Ali-Z0/2221_Underwater-Positioning-System/hard/3.3to5V.pdf

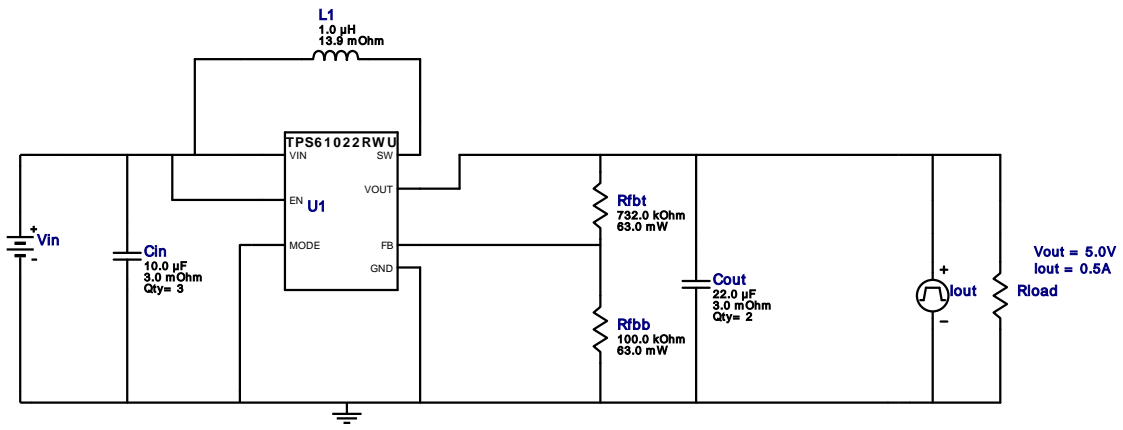
[picture p136: figure]
Vout = 5.0V Iout = 0.5A Cout; 22.0 µF 3.0 m Ohm Qty= 2; Rfbt 732.0 kOhm 63.0 m W; TPS6 1 0 2 2 RW U; GND; VOUT; MODE; VIN; Cin 10.0 µF 3.0 m Ohm Qty= 3; Rfbb 100.0 kOhm 63.0 m W; L1 1.0 µH 13.9 m Ohm; Vin; Iout; Rload

Copyright © 2023, Texas Instruments Incorporated | 1 | ti.com/webench

WEBENCH®
Design Report TPS61022RWUR : TPS61022RWUR 1V-3.7V to 5.00V @ 0.5A January 18, 2023 11:56:08 GMT-06:00

## WEBENCH ® Design Report

Design : 1 TPS61022RWUR
TPS61022RWUR 1V-3.7V to 5.00V @ 0.5A

VinMin = 1.0V
VinMax = 3.7V
Vout = 5.0V
Iout = 0.5A

Device = TPS61022RWUR
Topology = Boost_PassThrough Created = 2023-01-18 11:53:58.655 BOM Cost = $1.14
BOM Count = 9
Total Pd = 0.33W

### Design Alerts

Component Selection Information
1. The TPS61022 Device will operate in Pass-Through mode when Vin is greater than Vout. In Pass-Through mode, Vout is not regulated to the set Vout, instead Vout is Vin with the drop across the FET’s on-resistance and the DCR of the inductor. 2. This is a Boost Converter with 0.5V ultra-low input voltage. 3. The efficiency validation is done only for FPWM mode. Charts may be inaccurate for AutoMode at light loads and hence they are disabled for light loads.

## Electrical BOM

Name | Manufacturer | Part Number | Properties | Qty Price | Footprint
Cin | Kemet | C0805C106K8PACTU (http://capacitoredge.kemet.com/capedge2/DataSheet/Datasheet%2DC0805C106K8PACTU.pdf?pn%3DC0805C106K8PACTU) Series= X5R | Cap= 10.0 uF ESR= 3.0 mOhm VDC= 10.0 V IRMS= 11.43 A
3 | $0.03
| | | | | 0805 7 mm²
Cout | MuRata | GRM21BR61A226ME44L Series= X5R

Cap= 22.0 uF
ESR= 3.0 mOhm
VDC= 10.0 V
IRMS= 3.84 A

2 $0.09
0805 7 mm²
L1 | Bourns | SRN6045-1R0Y (http://www.bourns.com/data/global/pdfs/SRN6045.pdf) | L= 1.0 µH 13.9 mOhm | 1 | $0.25

SRN6045 64 mm²
Rfbb | Vishay-Dale | CRCW0402100KFKED (http://www.vishay.com/docs/20035/dcrcwe3.pdf) Series= CRCW..e3 | Res= 100.0 kOhm Power= 63.0 mW Tolerance= 1.0% | 1 | $0.01
0402 3 mm²
Rfbt | Vishay-Dale | CRCW0402732KFKED (http://www.vishay.com/docs/20035/dcrcwe3.pdf) Series= CRCW..e3 | Res= 732.0 kOhm Power= 63.0 mW Tolerance= 1.0% | 1 | $0.01
0402 3 mm²
U1 | Texas Instruments | TPS61022RWUR (http://www.ti.com/product/TPS61022) | Switcher | 1 | $0.60
RWU0007A 9 mm²

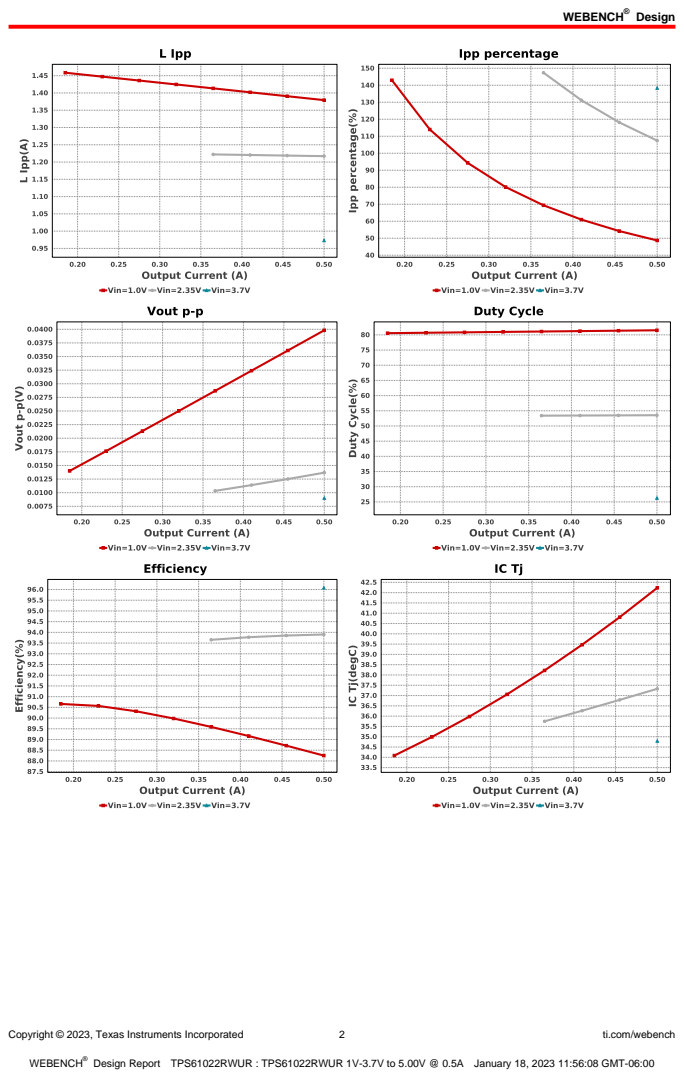
[picture p137: page 2]
Design; Copyright © 2023, Texas Instruments Incorporated; ti.com/webench

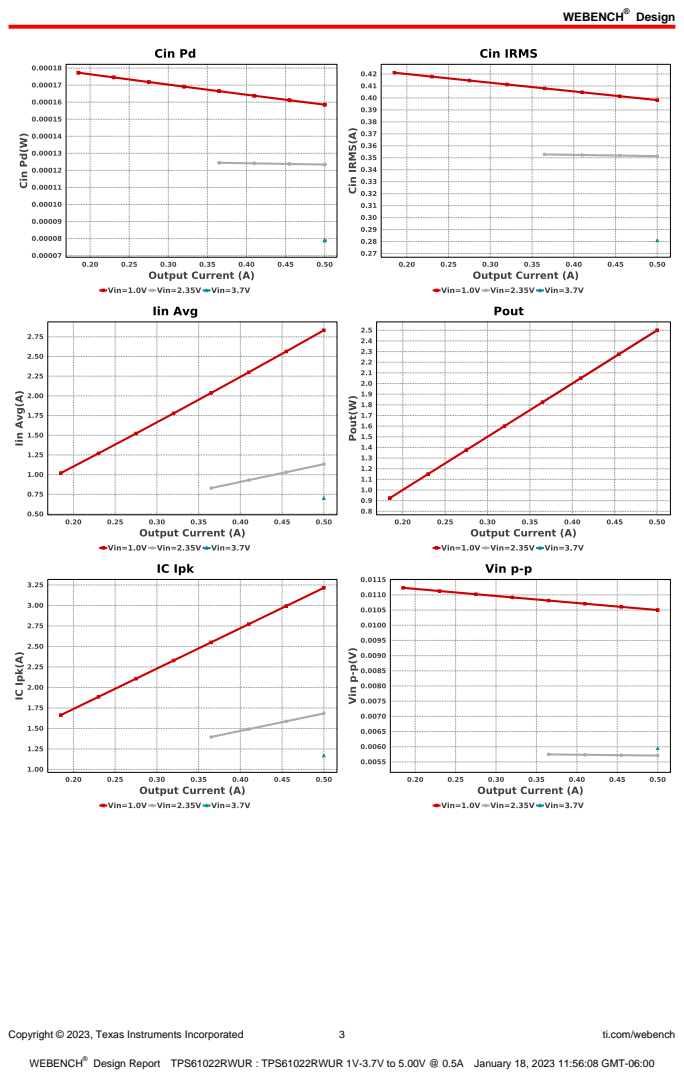
[picture p138: page 3]
Copyright © 2023, Texas Instruments Incorporated; ti.com/webench

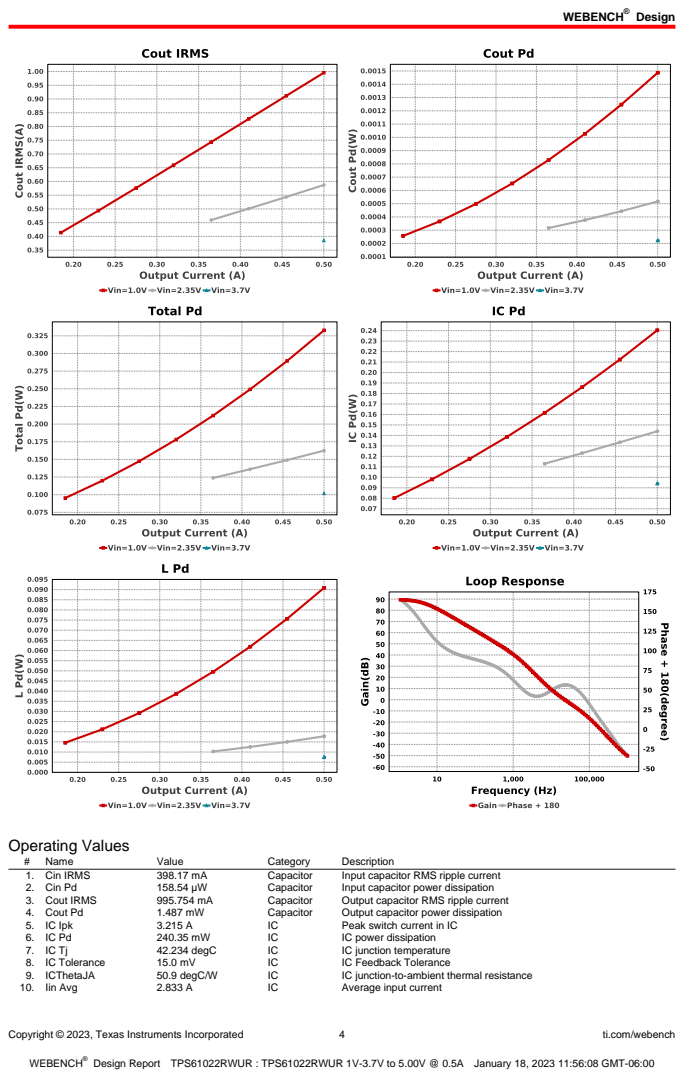
[picture p139: page 4]
Copyright © 2023, Texas Instruments Incorporated; ti.com/webench; Operating Values; Name; Value; Category; Description; 1. Cin IRMS; Capacitor; Input capacitor RMS ripple current; 2. Cin Pd; Input capacitor power dissipation; 3. Cout IRMS; Output capacitor RMS ripple current; 4. Cout Pd; Output capacitor power dissipation; 5. IC Ipk; Peak switch current in IC; IC power dissipation; 42.234 degC; IC junction temperature; 8. IC Tolerance; IC Feedback Tolerance; 9. ICThetaJA; 50.9 degC/W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

Copyright © 2023, Texas Instruments Incorporated | 5 | ti.com/webench
# | Name | Value | Category | Description

11. Ipp percentage | 48.689 % | Inductor | Inductor ripple current percentage (with respect to average inductor
| | | | current)
12. L Ipp | 1.379 A | Inductor | Peak-to-peak inductor ripple current
13. L Pd | 90.845 mW | Inductor | Inductor power dissipation
14. Cin Pd | 158.54 µW | Power | Input capacitor power dissipation
15. Cout Pd | 1.487 mW | Power | Output capacitor power dissipation
16. IC Pd | 240.35 mW | Power | IC power dissipation
17. L Pd | 90.845 mW | Power | Inductor power dissipation
18. Total Pd | 332.866 mW | Power | Total Power Dissipation
19. BOM Count | 9 | System
| | | Information | Total Design BOM count
20. Cross Freq | 8.104 kHz | System
| | | Information | Bode plot crossover frequency
21. Duty Cycle | 81.51 % | System
| | | Information | Duty cycle
22. Efficiency | 88.25 % | System
| | | Information | Steady state efficiency
23. FootPrint | 113.0 mm² | System
| | | Information | Total Foot Print Area of BOM components
24. Frequency | 541.532 kHz | System
| | | Information | Switching frequency
25. Gain Marg | -19.195 dB | System
| | | Information | Bode Plot Gain Margin
26. Iout | 500.0 mA | System
| | | Information | Iout operating point
27. Low Freq Gain | 77.425 dB | System
| | | Information | Gain at 1Hz
28. Mode | CCM | System
| | | Information | Conduction Mode
29. Phase Marg | 39.131 deg | System
| | | Information | Bode Plot Phase Margin
30. Pout | 2.5 W | System
| | | Information | Total output power
31. Total BOM | $1.14 | System
| | | Information | Total BOM Cost
32. Vin | 1.0 V | System
| | | Information | Vin operating point
33. Vin p-p | 10.502 mV | System
| | | Information | Peak-to-peak input voltage
34. Vout | 5.0 V | System
| | | Information | Operational Output Voltage
35. Vout Actual | 4.992 V | System
| | | Information | Vout Actual calculated based on selected voltage divider resistors
36. Vout Tolerance | 4.322 % | System
| | | Information | Vout Tolerance based on IC Tolerance (no load) and voltage divider resistors if applicable
37. Vout p-p | 39.821 mV | System
| | | Information | Peak-to-peak output ripple voltage

## Design Inputs

Name | Value | Description
| Iout | | 500.0 m | Maximum Output Current
VinMax | 3.7 | Maximum input voltage
VinMin | 1.0 | Minimum input voltage
Vout | 5.0 | Output Voltage
| base_pn | | TPS61022 | Base Product Number
source | DC | Input Source Type
Ta | 30.0 | Ambient temperature


Copyright © 2023, Texas Instruments Incorporated | 6 | ti.com/webench

## Assembly

## Component Testing

Some published data on components in datasheets such as Capacitor ESR and Inductor DC resistance is based on conservative values that will guarantee that the components always exceed the specification. For design purposes it is usually better to work with typical values. Since this data is not always available it is a good practice to measure the Capacitance and ESR values of Cin and Cout, and the inductance and DC resistance of L1 before assembly of the board. Any large discrepancies in values should be electrically simulated in WEBENCH to check for instabilities and thermally simulated in WebTHERM to make sure critical temperatures are not exceeded.

## Soldering Component to Board

If board assembly is done in house it is best to tack down one terminal of a component on the board then solder the other terminal. For surface mount parts with large tabs, such as the DPAK, the tab on the back of the package should be pre-tinned with solder, then tacked into place by one of the pins. To solder the tab town to the board place the iron down on the board while resting against the tab, heating both surfaces simultaneously. Apply light pressure to the top of the plastic case until the solder flows around the part and the part is flush with the PCB. If the solder is not flowing around the board you may need a higher wattage iron (generally 25W to 30W is enough).

## Initial Startup of Circuit

It is best to initially power up the board by setting the input supply voltage to the lowest operating input voltage 1.0V and set the input supply's current limit to zero. With the input supply off connect up the input supply to Vin and GND. Connect a digital volt meter and a load if needed to set the minimum Iout of the design from Vout and GND. Turn on the input supply and slowly turn up the current limit on the input supply. If the voltage starts to rise on the input supply continue increasing the input supply current limit while watching the output voltage. If the current increases on the input supply, but the voltage remains near zero, then there may be a short or a component misplaced on the board. Power down the board and visually inspect for solder bridges and recheck the diode and capacitor polarities. Once the power supply circuit is operational then more extensive testing may include full load testing, transient load and line tests to compare with simulation results.

## Load Testing

The setup is the same as the initial startup, except that an additional digital voltmeter is connected between Vin and GND, a load is connected between Vout and GND and a current meter is connected in series between Vout and the load. The load must be able to handle at least rated output power + 50% ( 7.5 watts for this design). Ideally the load is supplied in the form of a variable load test unit. It can also be done in the form of suitably large power resistors. When using an oscilloscope to measure waveforms on the prototype board, the ground leads of the oscilloscope probes should be as short as possible and the area of the loop formed by the ground lead should be kept to a minimum. This will help reduce ground lead inductance and eliminate EMI noise that is not actually present in the circuit.

## Design Assistance

1. Feature Highlights: 1. Device will operate in Pass-Through mode when Vin is greater than Vout. In Pass-Through mode, Vout is not regulated to the set Vout, instead Vout is Vin with the drop across the FET’s on-resistance and the DCR of the inductor. 2. Device will operate in PassThrough Mode When Vin is greater than Vout
2. Master key : 5CA681E4B8B8907C50E3CA5EF9C921E2[v1]
3. TPS61022 Product Folder : http://www.ti.com/product/TPS61022 : contains the data sheet and other resources.

Copyright © 2023, Texas Instruments Incorporated | 7 | ti.com/webench

Important Notice and Disclaimer

TI provides technical and reliability data (including datasheets), design resources (including reference designs), application or other design advice, web tools, safety information, and other resources AS IS and with all faults, and disclaims all warranties. These resources are intended for skilled developers designing with TI products. You are solely responsible for (1) selecting the appropriate TI products for your application, (2) designing, validating and testing your application, and (3) ensuring your application meets applicable standards, and any other safety, security, or other requirements.

These resources are subject to change without notice. TI grants you permission to use these resources only for development of an application that uses the TI products described in the resource. Other reproduction and display of these resources is prohibited. No license is granted to any other TI intellectual property right or to any third party intellectual property right. TI disclaims responsibility for, and you will fully indemnify TI and its representatives against, any claims, damages, costs, losses, and liabilities arising out of your use of these resources.

Providing these resources does not expand or otherwise alter TI's applicable Terms of Sale or other applicable terms available either on ti.com or provided in conjunction with TI products.
