Ali-Z0/2221_Underwater-Positioning-System/doc/listing/Mc32_sdFatGestC.pdf

C:\microchip\harmony\v2_06\apps\PROJ\Code-Principale\firmware\src\Mc32_sdFatGest.c

1 /* ************************************************************************** */ 2 /** Descriptive File Name 3

4 @Company
5 | | ETML-ES
6
7 @File Name 8 sd_fat_gest.c 9

10 @Summary
11 SD card fat system management 12

13 @Description
14 SD card fat system management 15 */

16 /* ************************************************************************** */ 17
18 /* ************************************************************************** */ 19 /* ************************************************************************** */
20 /* Section: Included Files | */
21 /* ************************************************************************** */ 22 /* ************************************************************************** */ 23
24 /* This section lists the other files that are included in this file. 25 */

26
27 #include "Mc32_sdFatGest.h" 28 #include <stdio.h>

29 #include "app.h" 30 #include "bno055_support.h" 31

32 /* ************************************************************************** */ 33 /* ************************************************************************** */
34 /* Section: File Scope or Global Data | */
35 /* ************************************************************************** */ 36 /* ************************************************************************** */ 37
38 APP_FAT_DATA COHERENT_ALIGNED appFatData; 39 /* ************************************************************************** */

40 /** Descriptive Data Item Name 41

42 @Summary
43 Brief one-line summary of the data item. 44

45 @Description
46 | | Full description, explaining the purpose and usage of data item.
47 | <p>
48 | | Additional description in consecutive paragraphs separated by HTML
49 | | paragraph breaks, as necessary.
50 | <p>
51 | Type "JavaDoc" in the "How Do I?" IDE toolbar for more information on tags. 52
53 @Remarks 54 | Any additional remarks 55 */

56
57
58 /* ************************************************************************** */ 59 /* ************************************************************************** */
60 // Section: Local Functions | */
61 /* ************************************************************************** */ 62 /* ************************************************************************** */ 63
64 /* ************************************************************************** */ 65
66
67
68 /* ************************************************************************** */ 69 /* ************************************************************************** */
70 // Section: Interface Functions | */
71 /* ************************************************************************** */ 72 /* ************************************************************************** */ 73
74 void sd_fat_task ( void )
75 {
76 | | /* The application task state machine */
77 | | switch(appFatData.state)
78 | {
79 | | case APP_MOUNT_DISK:
80 | | if(SYS_FS_Mount("/dev/mmcblka1", "/mnt/myDrive", FAT, 0, NULL) != 0)
81 | | {
82 | /* The disk could not be mounted. Try
83 | * mounting again untill success. */
84
85 | appFatData.state = APP_MOUNT_DISK; 86 | }
87 | else 88 | {
89 | /* Mount was successful. Unmount the disk, for testing. */
90
91 | appFatData.state = APP_SET_CURRENT_DRIVE; 92 | }
93 | break; 94
95 | | case APP_SET_CURRENT_DRIVE:
96 | | if(SYS_FS_CurrentDriveSet("/mnt/myDrive") == SYS_FS_RES_FAILURE)
97 | | {
98 | /* Error while setting current drive */
99 | appFatData.state = APP_ERROR; 100 | }
101 | else 102 | {
103 | /* Open a file for reading. */
104 | appFatData.state = APP_IDLE; 105 | }
106 | | break;

107
108 | | | | | | case APP_WRITE_MEASURE_FILE:
109 | appFatData.fileHandle = SYS_FS_FileOpen("MESURES.csv", 110 | (SYS_FS_FILE_OPEN_APPEND_PLUS)); 111 | if(appFatData.fileHandle == SYS_FS_HANDLE_INVALID)
112 | | | | | | {
113 | | | | | | /* Could not open the file. Error out*/
114 | appFatData.state = APP_ERROR; 115 | }
116 | else 117 | {
118 | | | | | | /* Create a directory. */
119 | appFatData.state = APP_WRITE_TO_MEASURE_FILE; 120 | }
121 | break; 122
123 | case APP_WRITE_TO_MEASURE_FILE: 124 | /* If read was success, try writing to the new file */
125 | | | | | | if(SYS_FS_FileStringPut(appFatData.fileHandle, appFatData.data) == -1)
126 | | | | | | {
127 | /* Write was not successful. Close the file 128 | * and error out.*/
129 | SYS_FS_FileClose(appFatData.fileHandle); 130 | appFatData.state = APP_ERROR; 131 | }
132 | else 133 | {
134 | appFatData.state = APP_CLOSE_FILE; 135 | }
136 | break; 137
138 | case APP_CLOSE_FILE: 139 | /* Close both files */
140 | SYS_FS_FileClose(appFatData.fileHandle); 141 | /* The test was successful. Lets idle. */
142 | appFatData.state = APP_IDLE; 143 | break; 144
145 | case APP_IDLE: 146 | /* The appliction comes here when the demo 147 | * has completed successfully. Switch on
148 | | | | | | * green LED. */
149 | //BSP_LEDOn(APP_SUCCESS_LED); 150 | LED_ROff(); 151 | break; 152 | case APP_ERROR: 153 | /* The appliction comes here when the demo 154 | * has failed. Switch on the red LED.*/
155 | //BSP_LEDOn(APP_FAILURE_LED); 156 | LED_ROn(); 157 | break; 158 | default: 159 | break; 160
161 | | | | | case APP_UNMOUNT_DISK:
162 | | | | | if(SYS_FS_Unmount("/mnt/myDrive") != 0)
163 | | | | | {
164 | | | | | /* The disk could not be un mounted. Try
165 | | | | | * un mounting again untill success. */
166
167 | appFatData.state = APP_UNMOUNT_DISK; 168 | }
169 | else 170 | {
171 | | | | | /* UnMount was successful. Mount the disk again */
172 | appFatData.state = APP_IDLE; 173 | }
174 | break; 175
176 | }
177
178 // SYS_FS_Tasks(); 179 } //End of APP_Tasks 180

181 void sd_BNO_scheduleWrite (s_bno055_data * data) 182 {
183 | | | | | /* If sd Card available */
184 | | | | | if(appFatData.state == APP_IDLE)
185 | {
186 | | | | | /* Next state : write to file */
187 | appFatData.state = APP_WRITE_MEASURE_FILE; 188 | /* Write the buffer */
189 | sprintf(appFatData.data, "%d;%d0;%f;%.4f;%.4f;%.4f;%.4f;%.4f;%.4f;%.4f;%.4f;%.4f;%.4f;%.4f;%.4f;%.4f;%.4f;%.4f;%d;%d;%d;%d;" 190 | ,data->flagImportantMeas, (data->d_time), data->pressure, data->gravity.x, data->gravity.y, data->gravity.z, data->gyro.x, data->gyro.y, data->gyro.z 191 | ,data->mag.x, data->mag.y, data->mag.z, data->linear_accel.x, data->linear_accel.y, data->linear_accel.z 192 | ,data->euler.h, data->euler.p, data->euler.r, data->quaternion.w, data->quaternion.x, data->quaternion.y, data->quaternion.z); 193 | /* Compute the number of bytes to send */
194 | appFatData.nBytesToWrite = strlen(appFatData.data); 195 | }

196 }
197
198 APP_FAT_STATES sd_getState( void )
199 {
200 return appFatData.state; 201 }

202
203 void sd_setState( APP_FAT_STATES newState ) 204 {
205 appFatData.state = newState; 206 }

207
208 /* ***************************************************************************** 209 End of File 210 */

211
