Ali-Z0/2221_Underwater-Positioning-System/doc/Presentations/Etude/presentation-main.pdf

# PRÉSENTATION ÉTUDE

Localisation sous-marine 2221
Système de logging pour algorithme de localisation sous-marine

Dérnière MAJ : 8 février 2023

Ali Zoubir

ETML-ES
Génie électrique

1. Introduction
2. Conception
3. Schématique
4. Conclusion
5. Questions ?

## INTRODUCTION

Voici les éléments développés lors de l’étude : Documentation
Rédaction d’un rapport de projet.
Conception
Diagrammes et description de fonctionnement plus pointus. Mécanique
Réflexions idées et perspectives quant à la mécanique du module. Schématique
Développement d’un schéma électrique complet avec hiérarchie de fichiers.

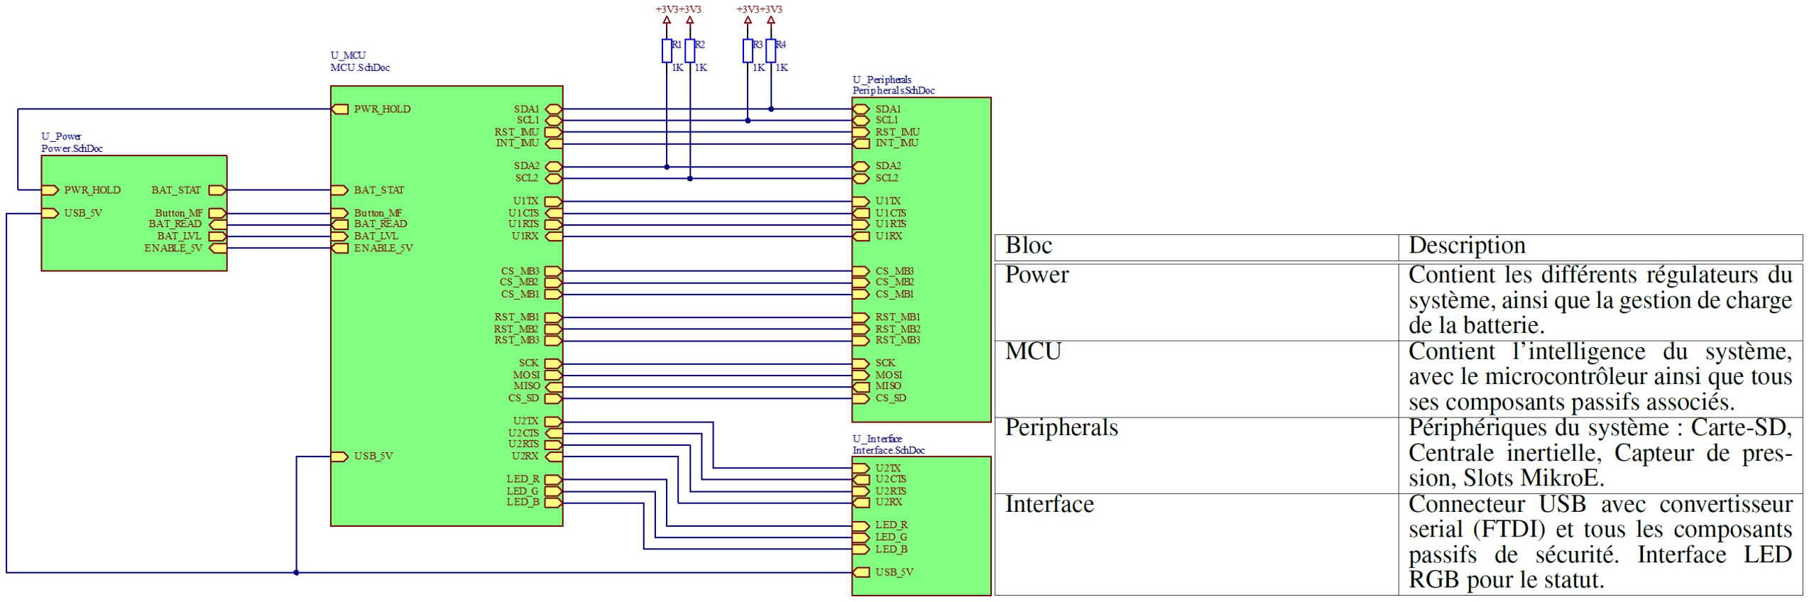
[picture p141: figure]

Figure : Schéma bloc du système à jour

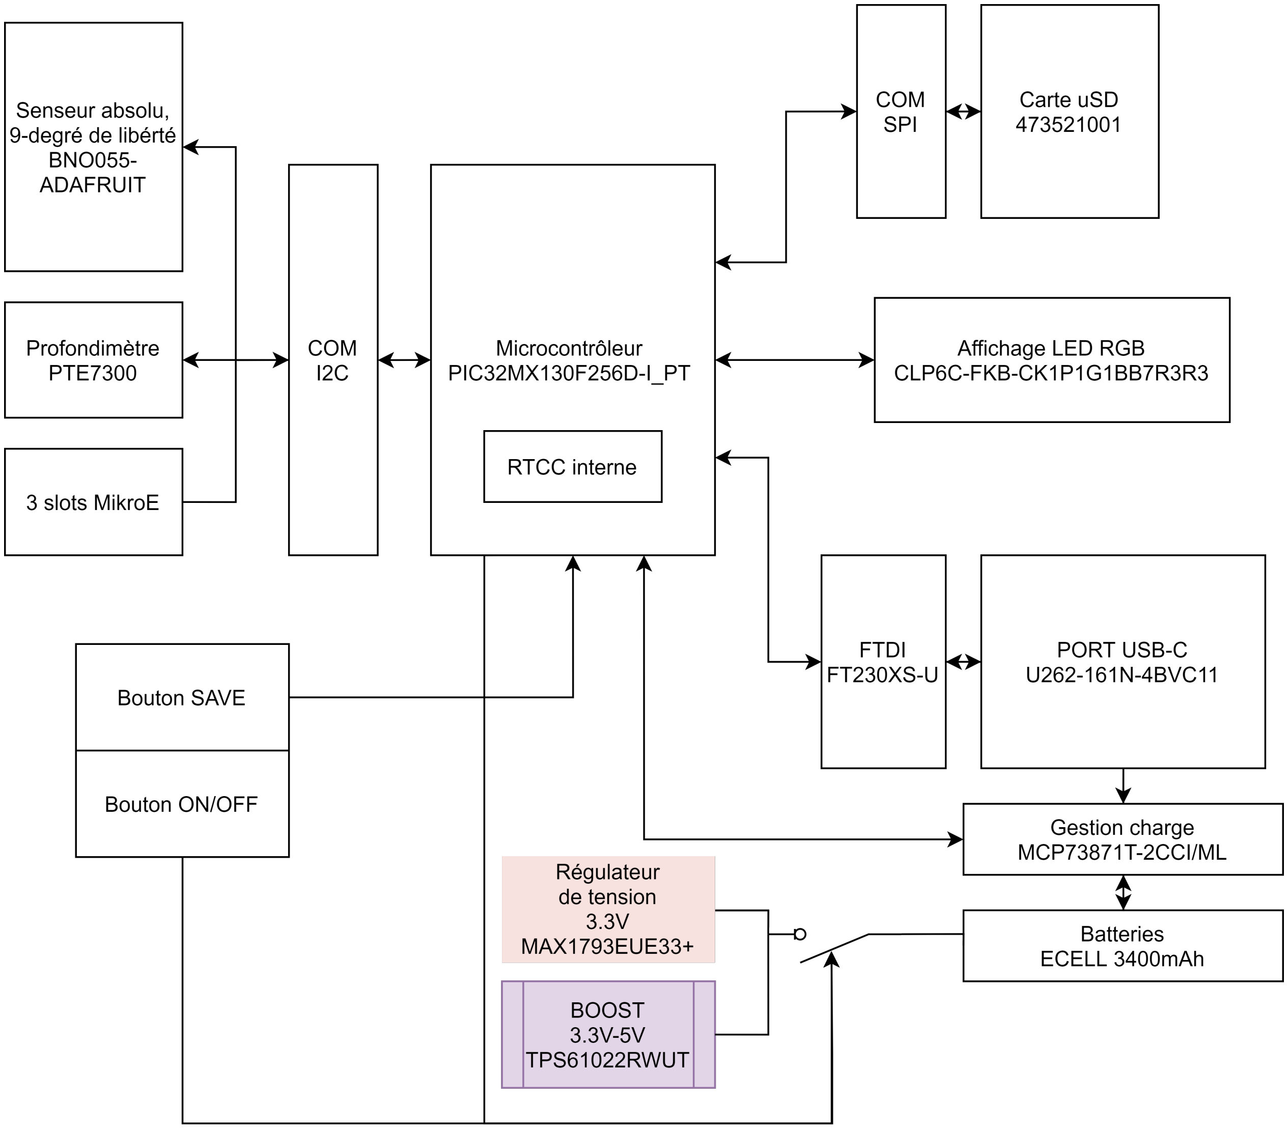
[picture p142: figure]

Figure : Schéma bloc détaillé | 6

## CONCEPTION

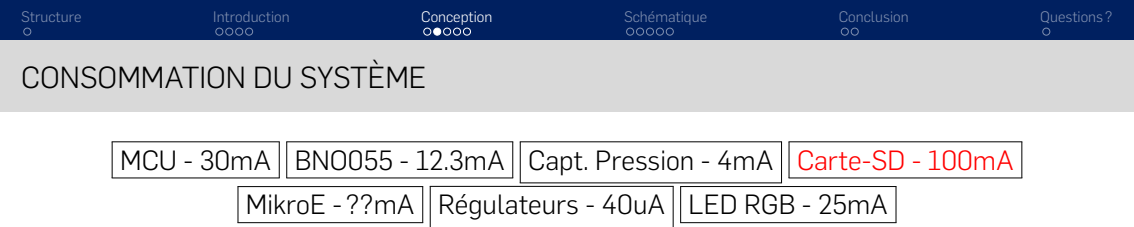
[picture p143: figure]
CONSOMMATION DU SYSTÈME; MCU - 30mA; BNO055 - 12.3mA; Capt. Pression - 4mA; Carte-SD - 100mA; MikroE - ??mA; Régulateurs - 40uA; LED RGB - 25mA

Total : 171,34mA

Capacite = Consommationtot ∗ Temps | (1)

Pour 1 expédition (2h) : ∼342.68mAh
Accu 3400mAh (Commande commune) : ∼20h
C’est un temps largement suffisant pour la durée de plusieurs expéditions, néanmoins la RTCC du microcontrôleur requiert d’être alimentée en permanence, un mécanisme de veille doit donc être mis en place.

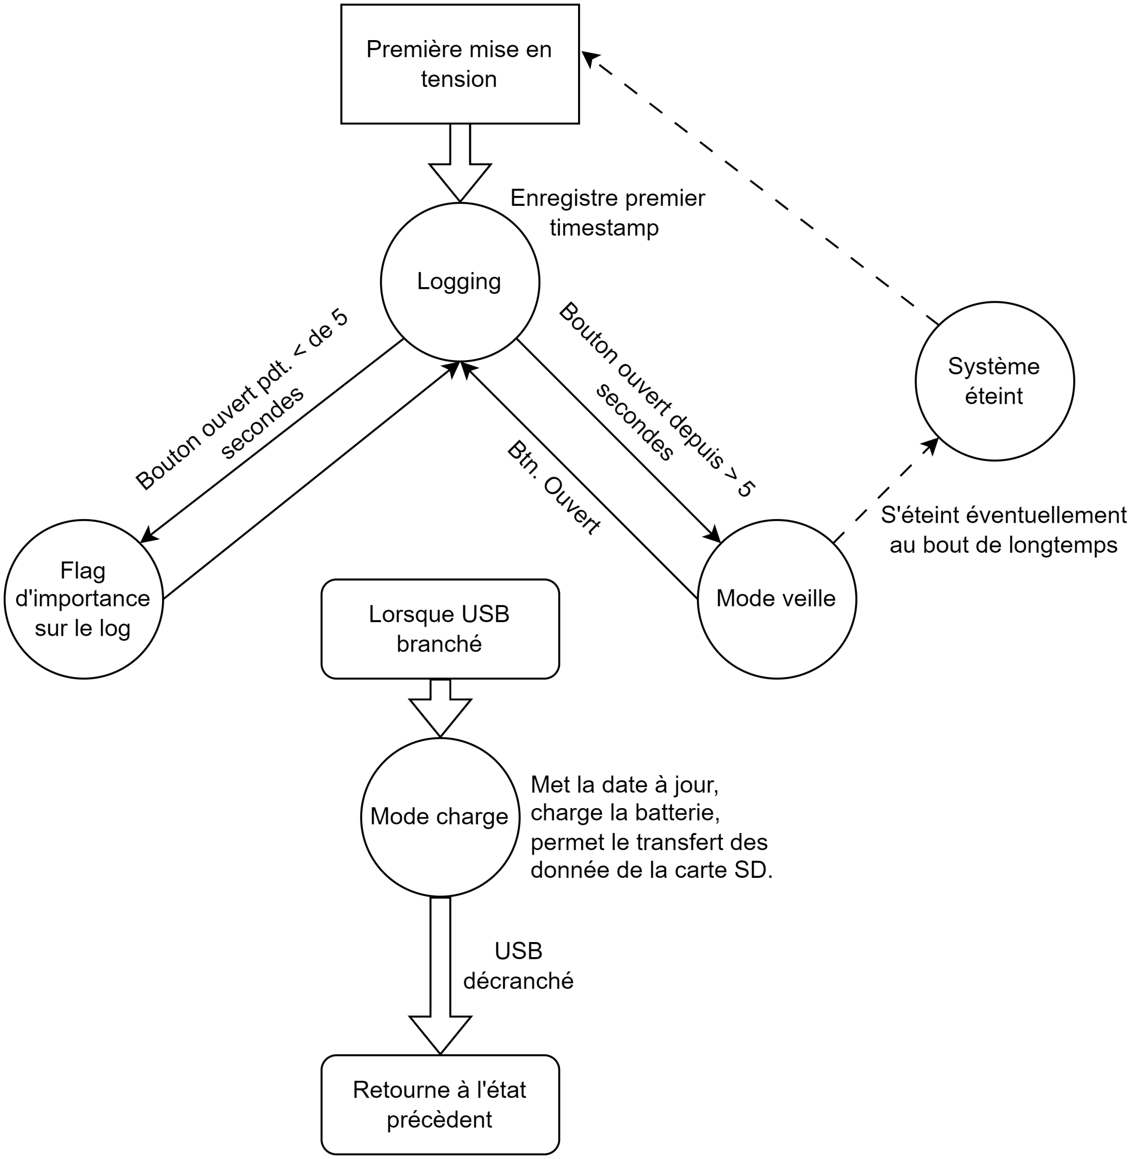
[picture p144: figure]

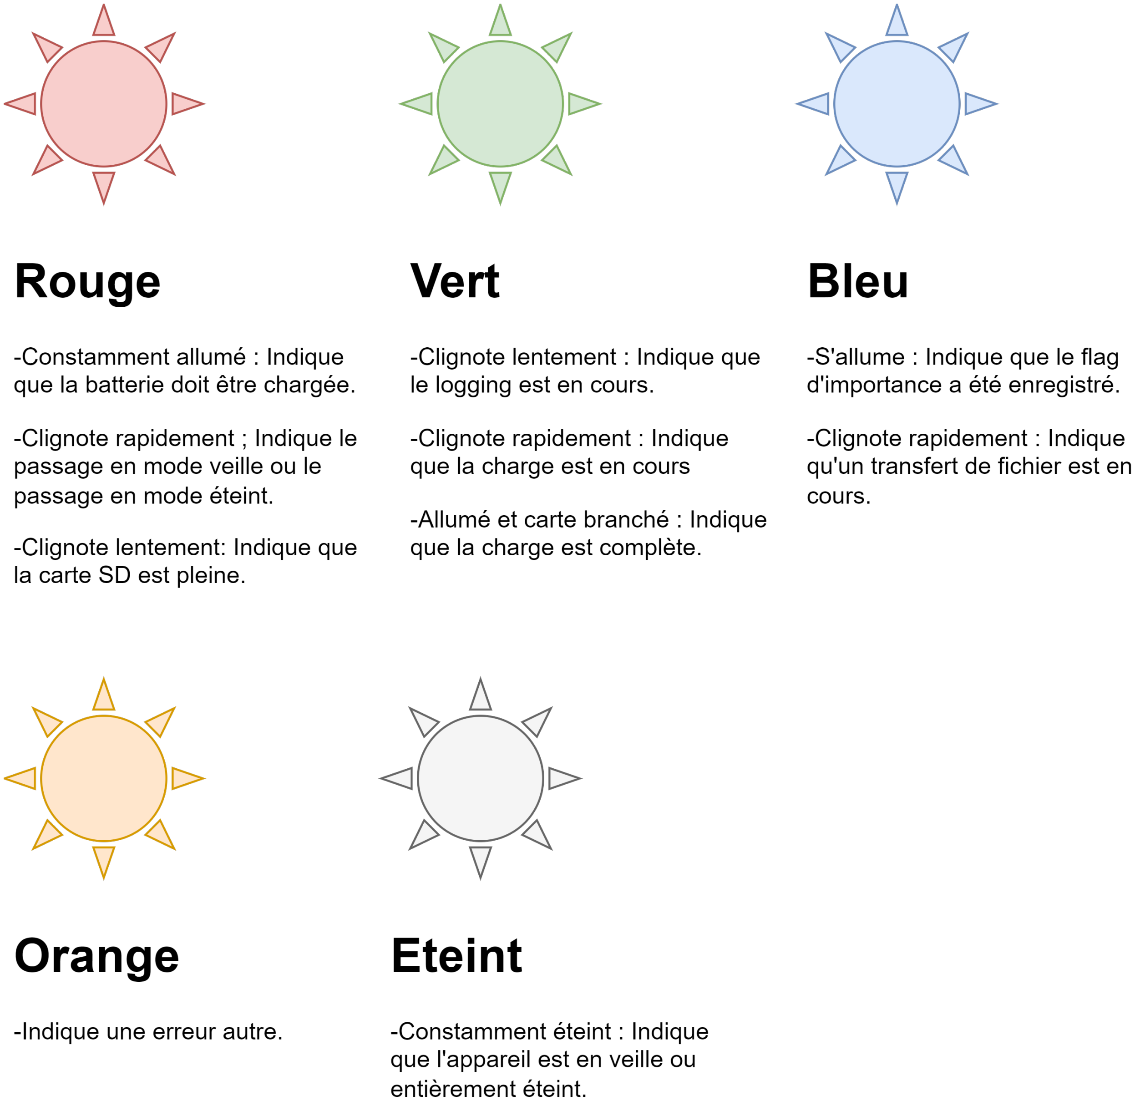
[picture p145: figure]

Figure : Status LED d’interface | 10

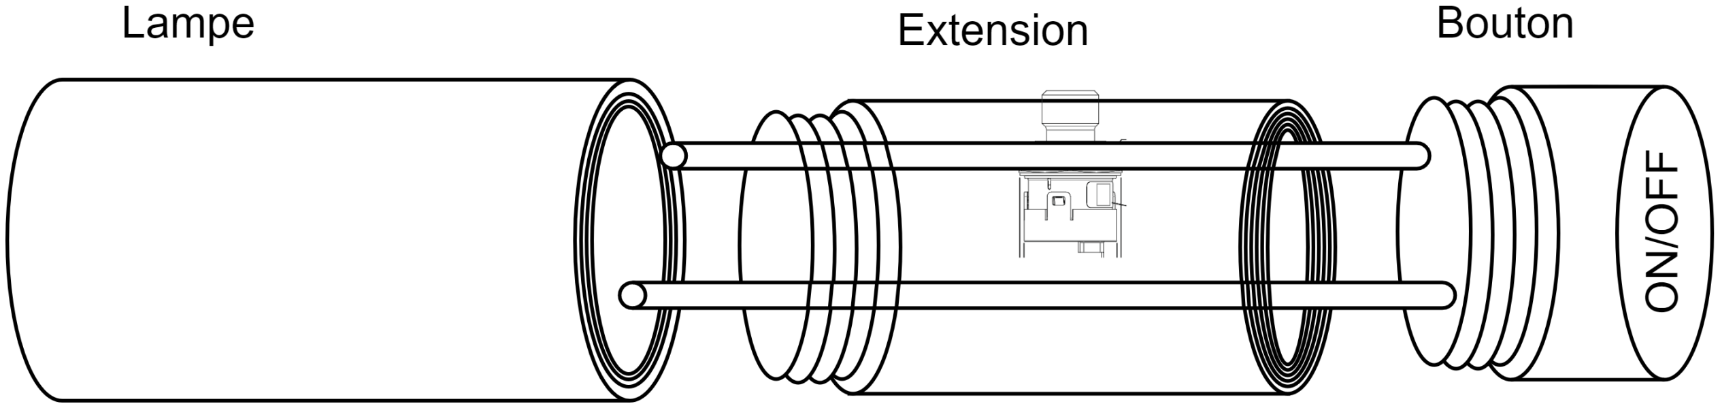
[picture p146: figure]

Figure : Schéma bloc du système à jour


## SCHÉMATIQUE

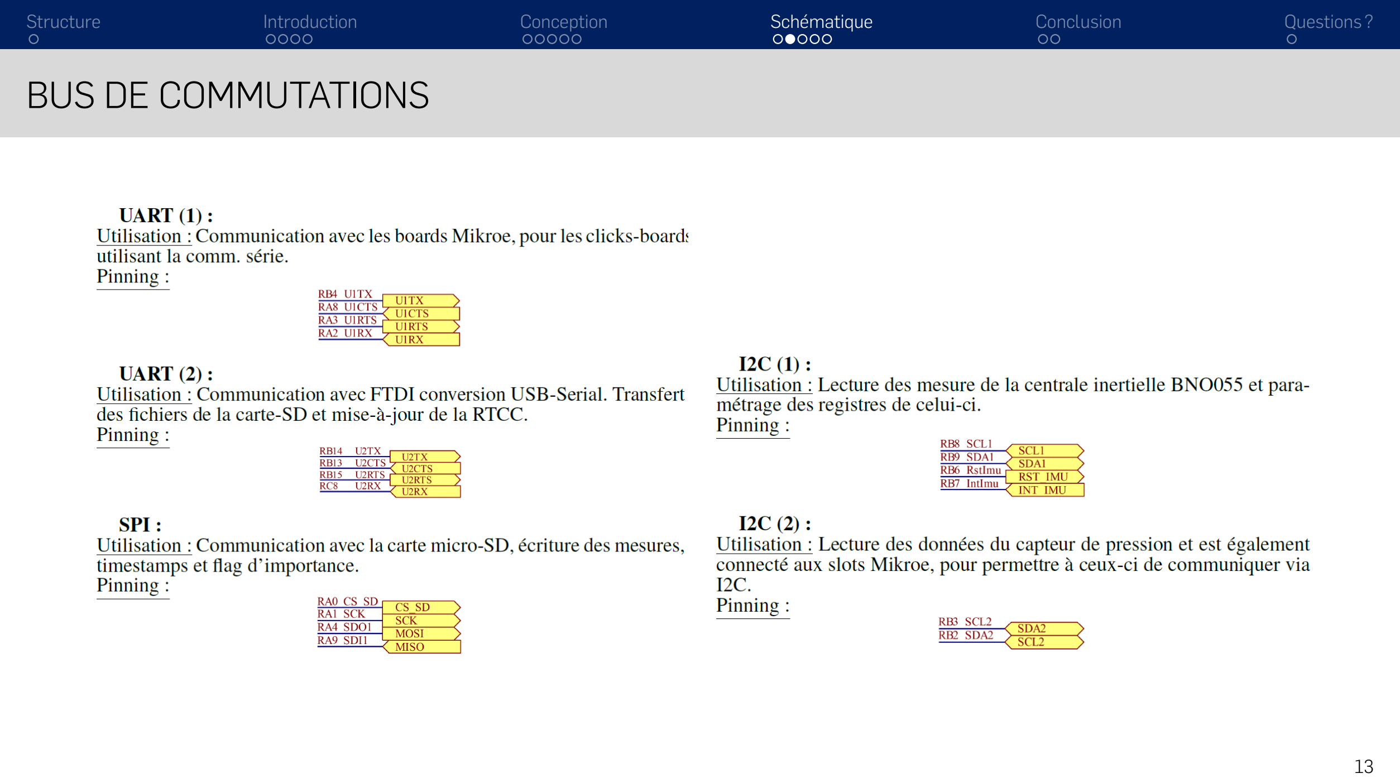
[picture p147: page 13]

BUS DE COMMUTATIONS

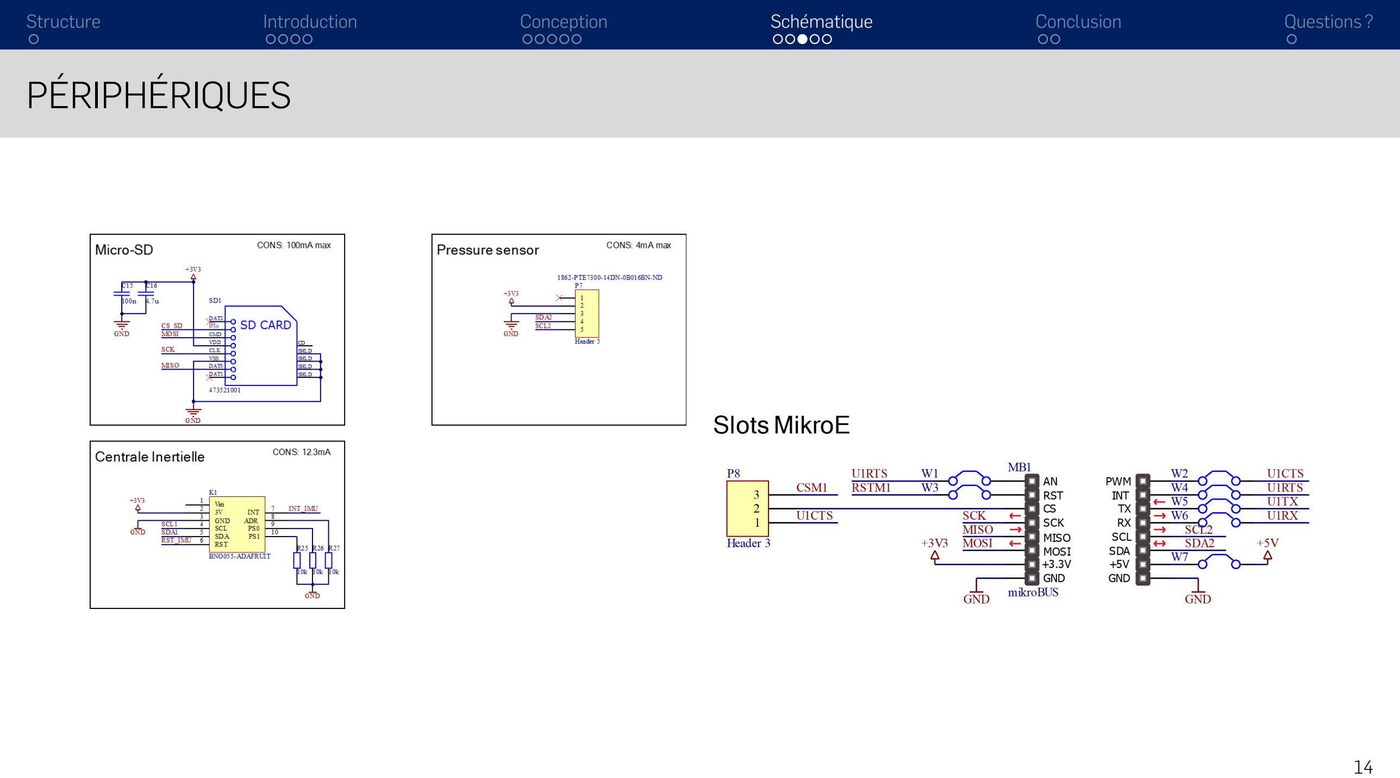
[picture p148: page 14]

PÉRIPHÉRIQUES


C = 3400mAh ratioterm = 0.05 | ratiochrg = 0.1
Iterm = C ∗ ratiochrg | (2)
D’après 2, Iterm = 170mA.

### Rprog3 =

1000V
Iterm

(3)
Rprog3 = 5k88Ω E12 =⇒ 6k2Ω.

### Rprog1 =

1000V

### C ∗ ratiochrg

(4)
Rprog1 = 2k94Ω E12 =⇒ 2k2Ω. | 15

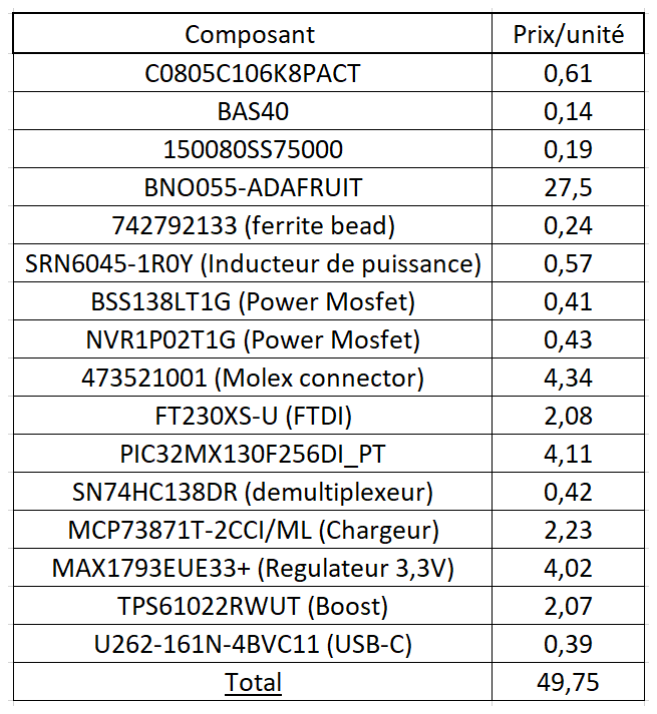
[picture p149: figure]

## CONCLUSION

Lors du développement de la schématique, je n’ai pas eu de grands dimensionnements à faire mais plutôt dû mettre en place des mécanismes permettant la communication avec tous les senseurs et périphériques du système.
Désormais il vas falloir préparer la création du PCB, en contrôlant les footprints du circuit et développer d’avantage l’aspect mécanique du projet.

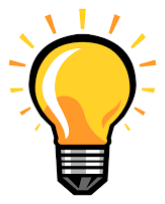
[picture p150: figure]

## QUESTIONS ?
