Ali-Z0/2221_Underwater-Positioning-System/mec/pcb/2221_PCB_MechDims2.pdf

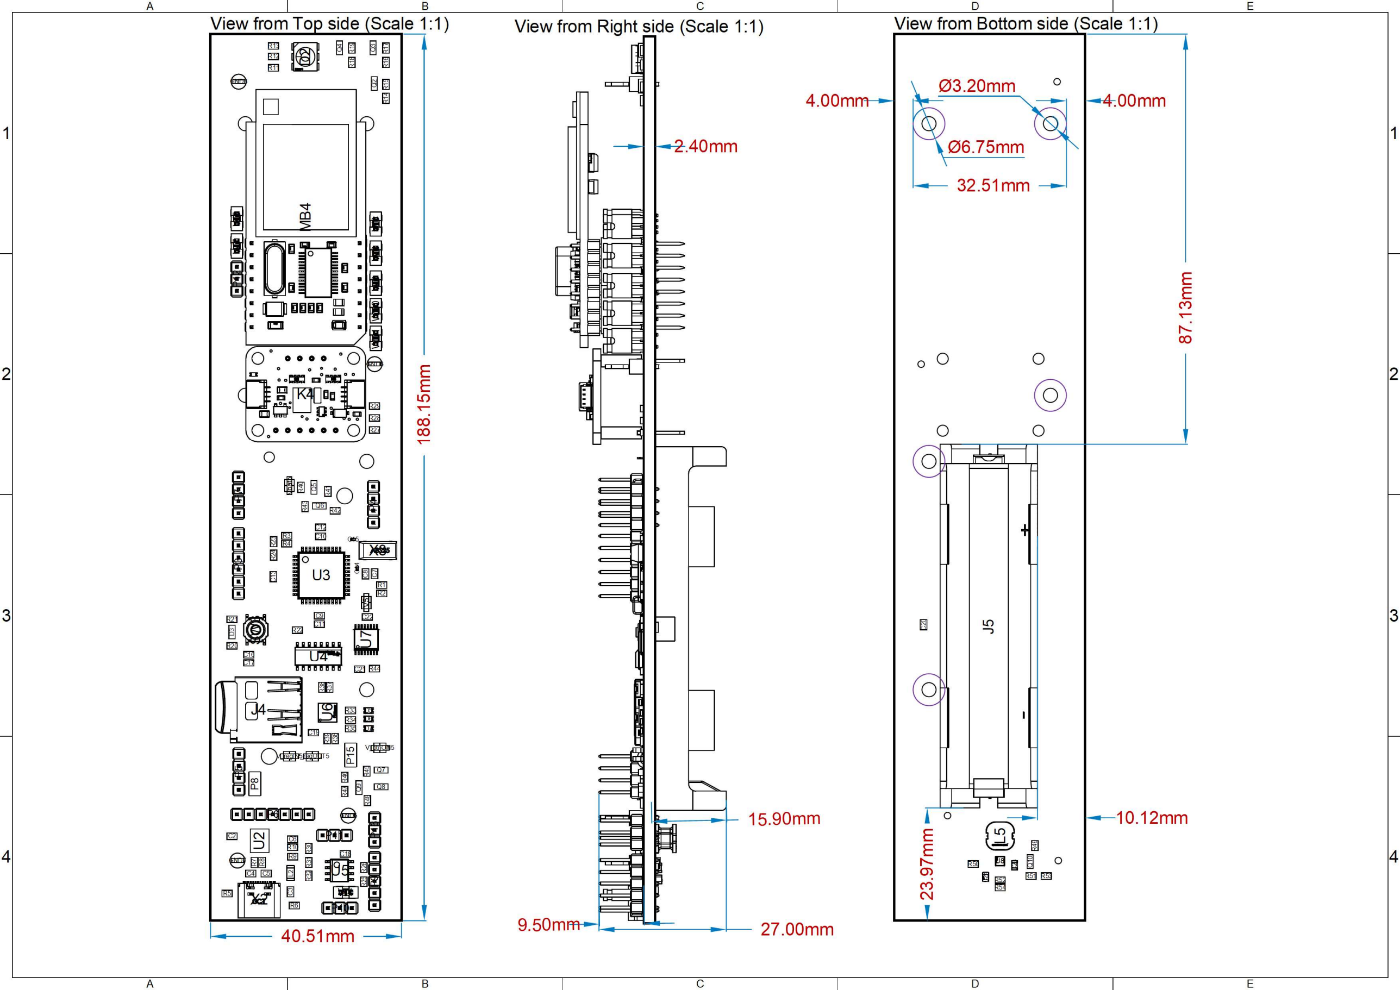
[picture p160: page 1]
