Ali-Z0/2221_Underwater-Positioning-System/doc/Presentations/Pre-etude/Pré-étude/Images/plot-eps-converted-to.pdf

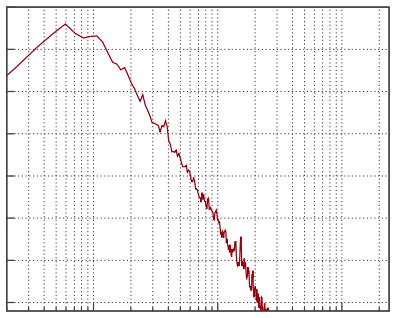
[picture p161: figure]
