Ali-Z0/2221_Underwater-Positioning-System/doc/composants/9DOF-BNO055/Sorties/EUL.PNG

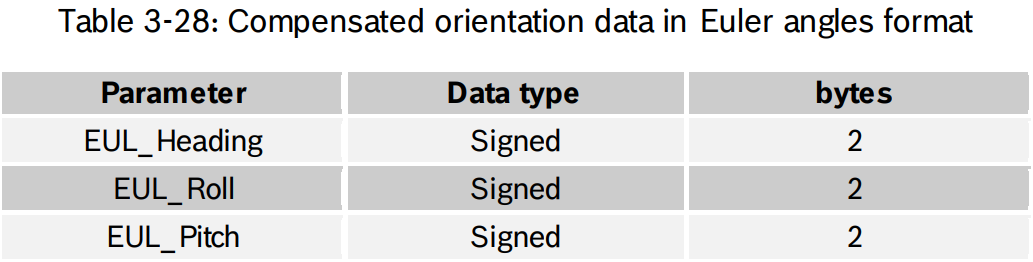
doc/composants/9DOF-BNO055/Sorties/EUL.PNG
