Ali-Z0/2221_Underwater-Positioning-System/doc/composants/9DOF-BNO055/Sorties/MAG.PNG

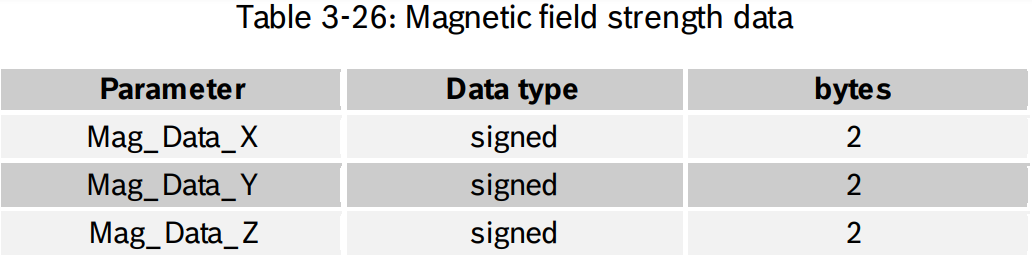
doc/composants/9DOF-BNO055/Sorties/MAG.PNG
