Ali-Z0/2221_Underwater-Positioning-System/doc/composants/SD-CardReader-MikroE/MMC_SD Board Examples/MMC_SD Board Examples for AVR microcontroller/mikroBasic PRO for AVR/MMC-SD Board.jpg

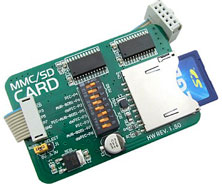
doc/composants/SD-CardReader-MikroE/MMC_SD Board Examples/MMC_SD Board Examples for AVR microcontroller/mikroBasic PRO for AVR/MMC-SD Board.jpg
