Ali-Z0/2221_Underwater-Positioning-System/doc/Presentations/Pre-etude/Pré-étude/Images/Altium-blocks.png

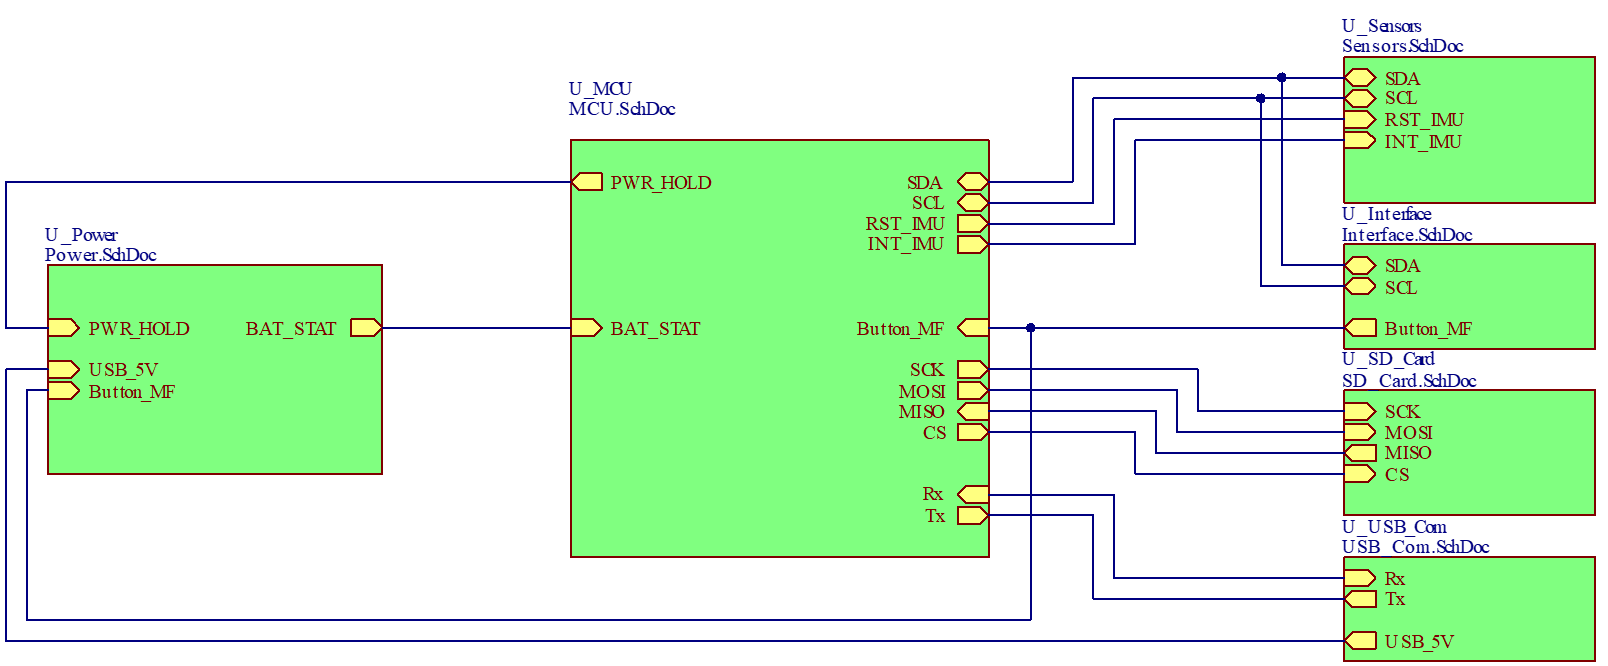
doc/Presentations/Pre-etude/Pré-étude/Images/Altium-blocks.png
