Ali-Z0/2221_Underwater-Positioning-System/doc/Presentations/Pre-etude/Pré-étude/Images/chemin.jpg

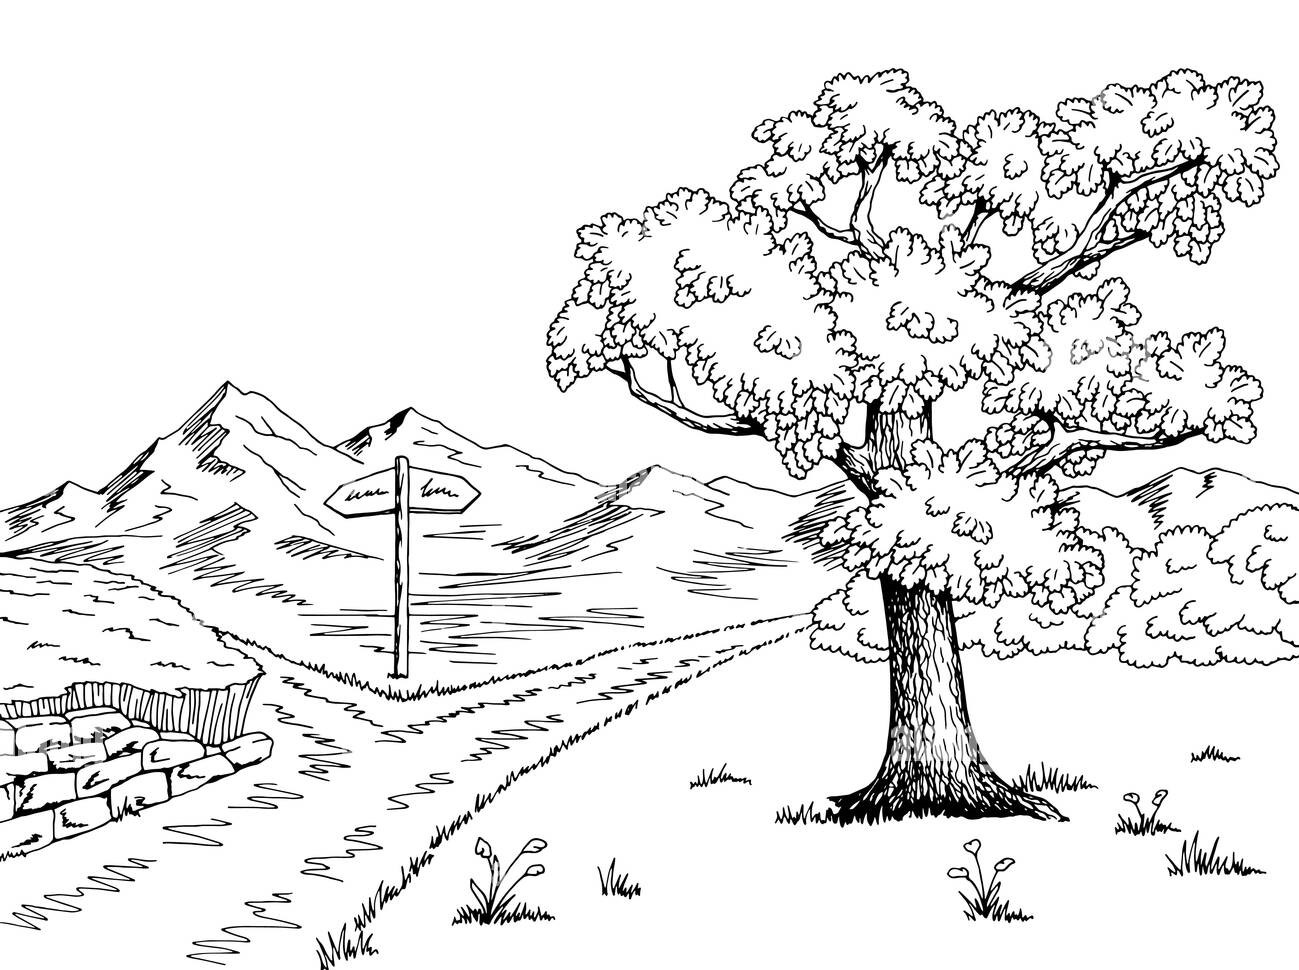
doc/Presentations/Pre-etude/Pré-étude/Images/chemin.jpg
