Ali-Z0/2221_Underwater-Positioning-System/doc/rapport/CDC/Figures/l_scubapro-tauchlampe-850-wide.jpg

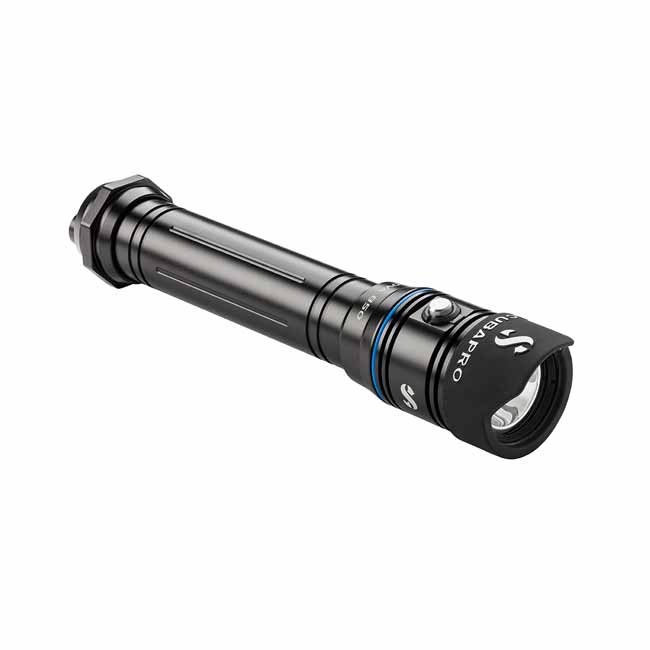
doc/rapport/CDC/Figures/l_scubapro-tauchlampe-850-wide.jpg
