Ali-Z0/2221_Underwater-Positioning-System/doc/rapport/Rapport/Mesures/PuttYSerComm.png

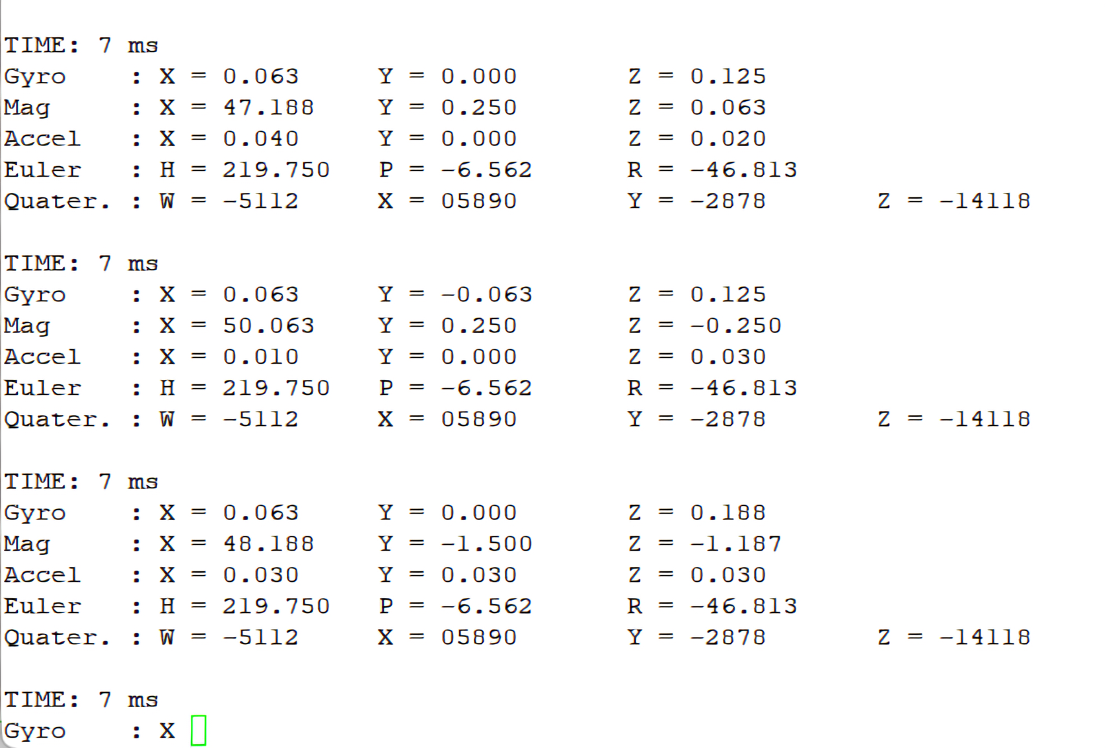
doc/rapport/Rapport/Mesures/PuttYSerComm.png
