Ali-Z0/2221_Underwater-Positioning-System/doc/rapport/Rapport/Mesures/Tension3.3V.PNG

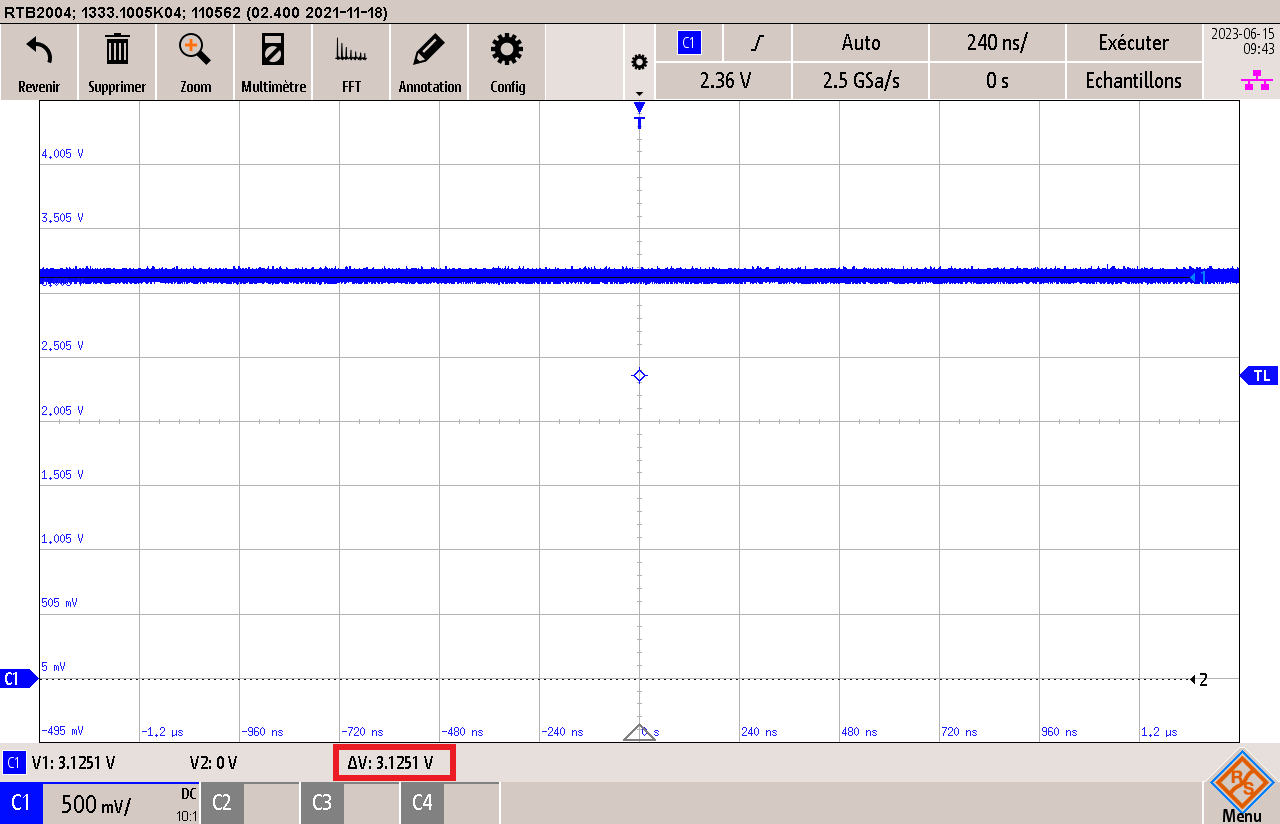
doc/rapport/Rapport/Mesures/Tension3.3V.PNG
