Ali-Z0/2221_Underwater-Positioning-System/doc/rapport/Rapport/Mesures/Tension5V.PNG

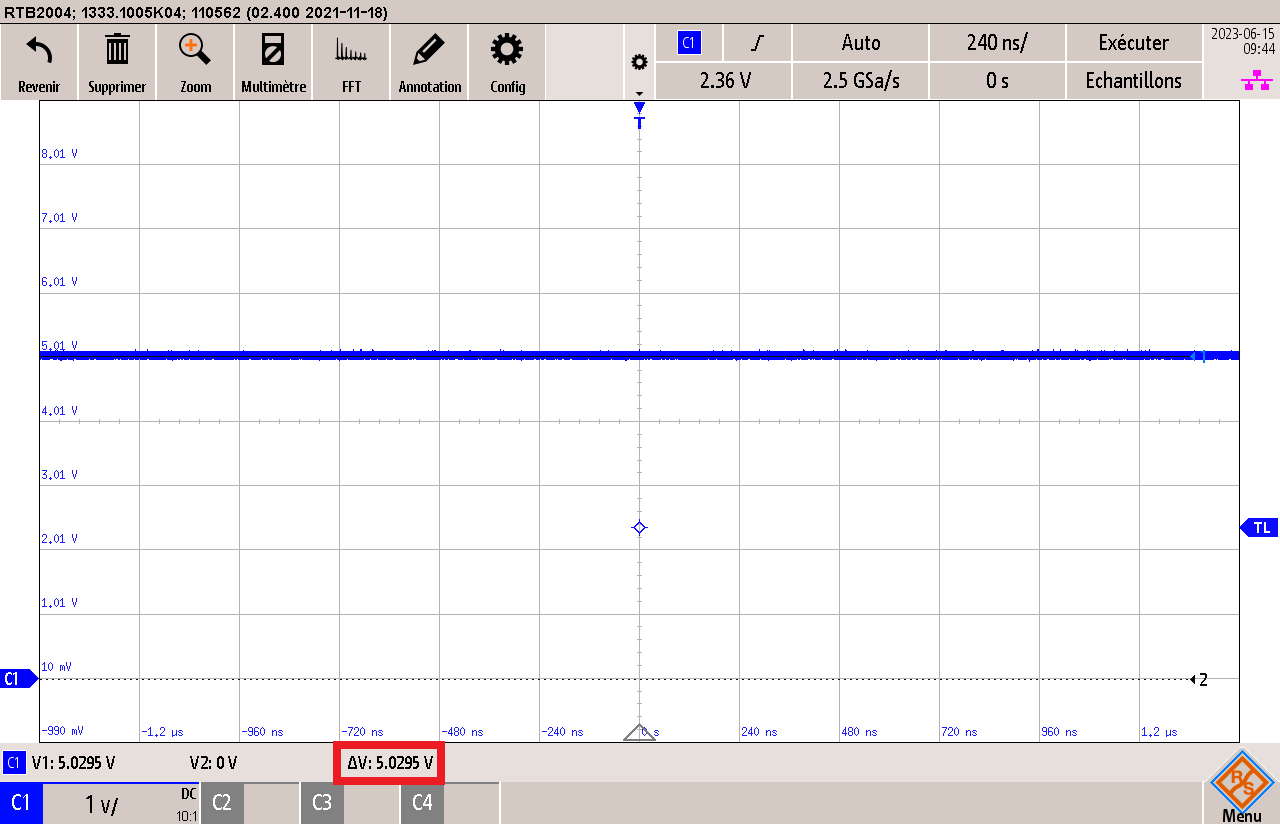
doc/rapport/Rapport/Mesures/Tension5V.PNG
