Ali-Z0/2221_Underwater-Positioning-System/doc/references/Figures/CaptPression.png

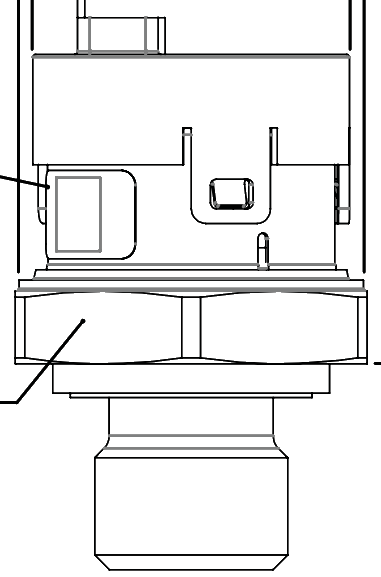
doc/references/Figures/CaptPression.png
