Ali-Z0/2221_Underwater-Positioning-System/doc/references/Figures/MecaniqueProto2.png

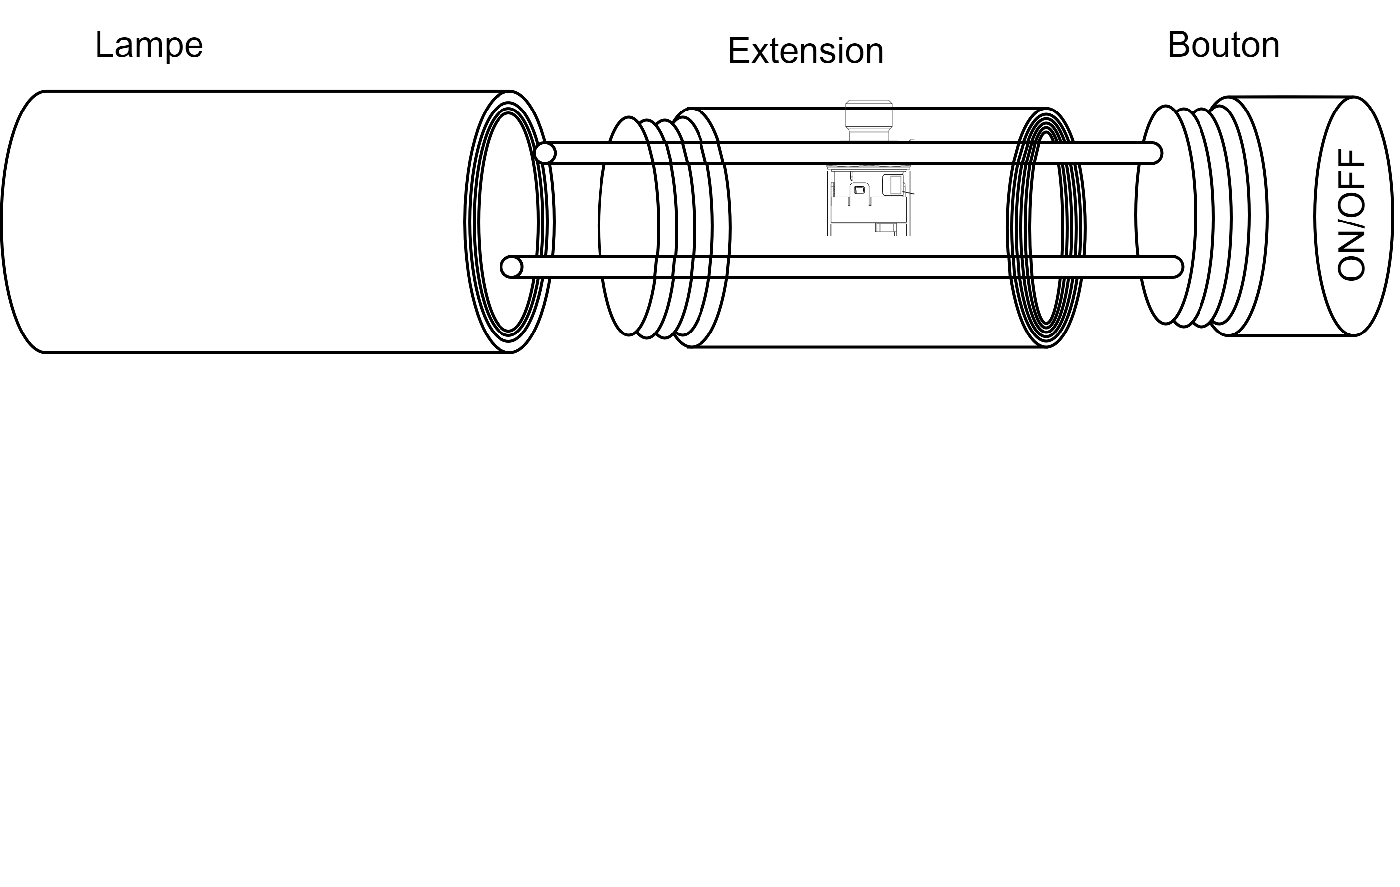
doc/references/Figures/MecaniqueProto2.png
