Ali-Z0/2221_Underwater-Positioning-System/doc/2221_Schematique.pdf

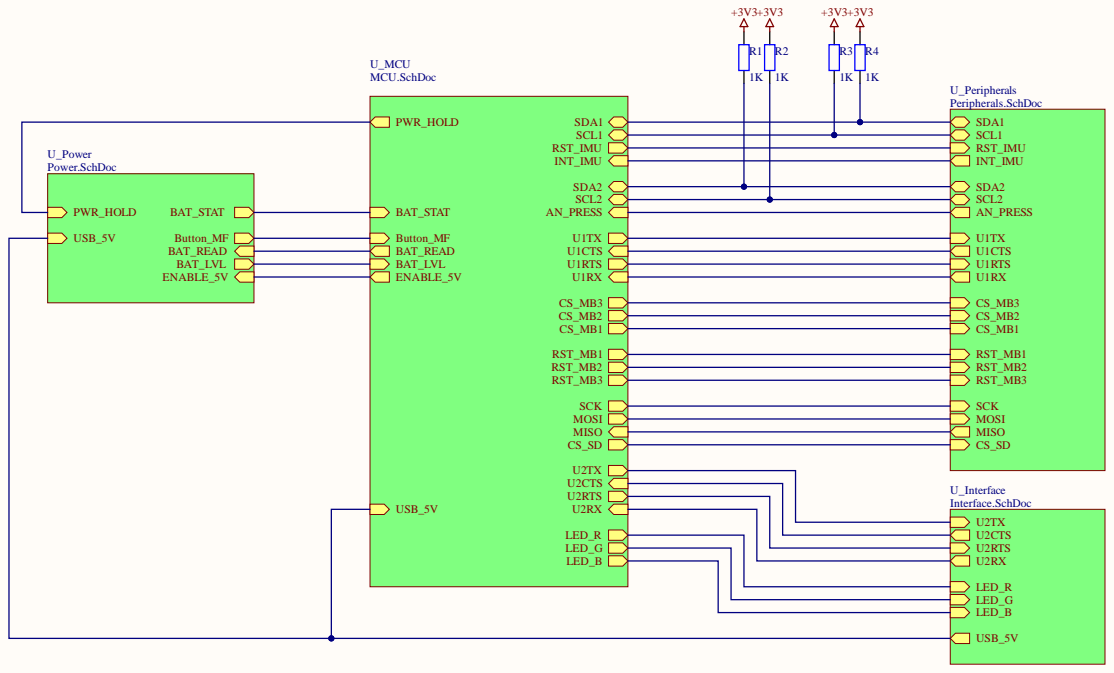
[picture p207: page 1]

SchemaBloc. SchDoc Fichier :

Date : 08.02.2023 | Version : V0

Heure : 14:08:45 | Ali Zoubir Auteur :
Avenue Recordon 1 1004 Lausanne Switzerland | Projet : 2221_Localisa tionSousMarine.PrjPcb | No : 2221

Nb feuilles | Feuille n°

Chemin : C:\Users\alizoubir\Documents\ETML-

ES-2eme\PROJ\2221_LocalisationSousMarine\hard\2221_LocalisationSousMarine\Schemati

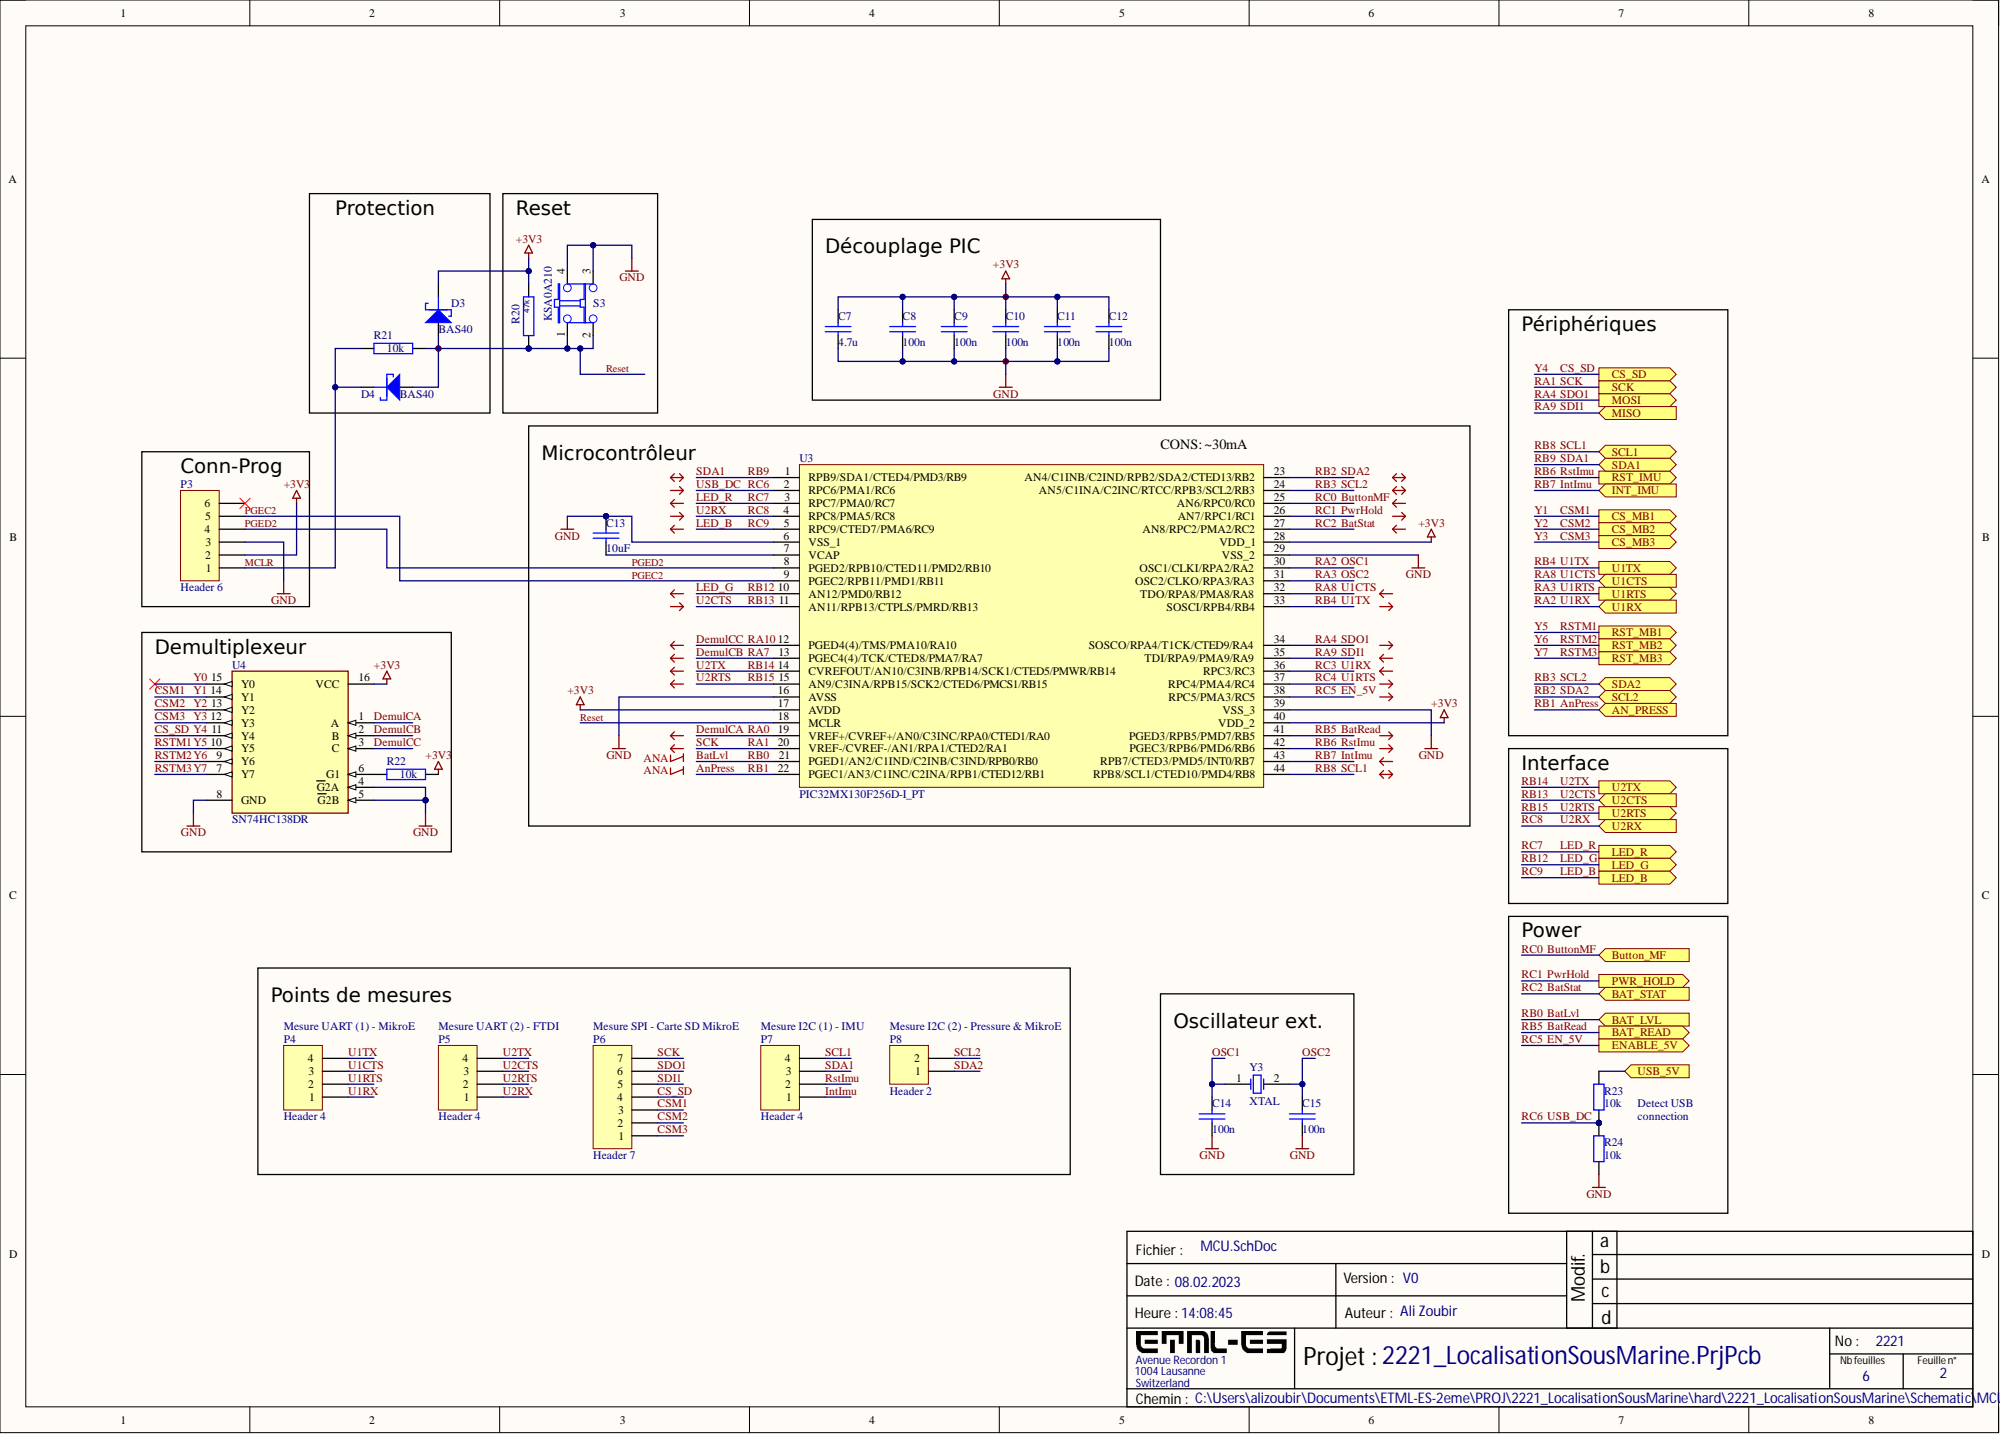
[picture p208: page 2]

P G E D 2 | C1 3 L E D _B RC9 | 5 | 2 7 RC2 BatSt

ure SPI - Carte SD Mi

MCU . SchDoc Fichier :

Date : 08.02.2023 | Version : V0

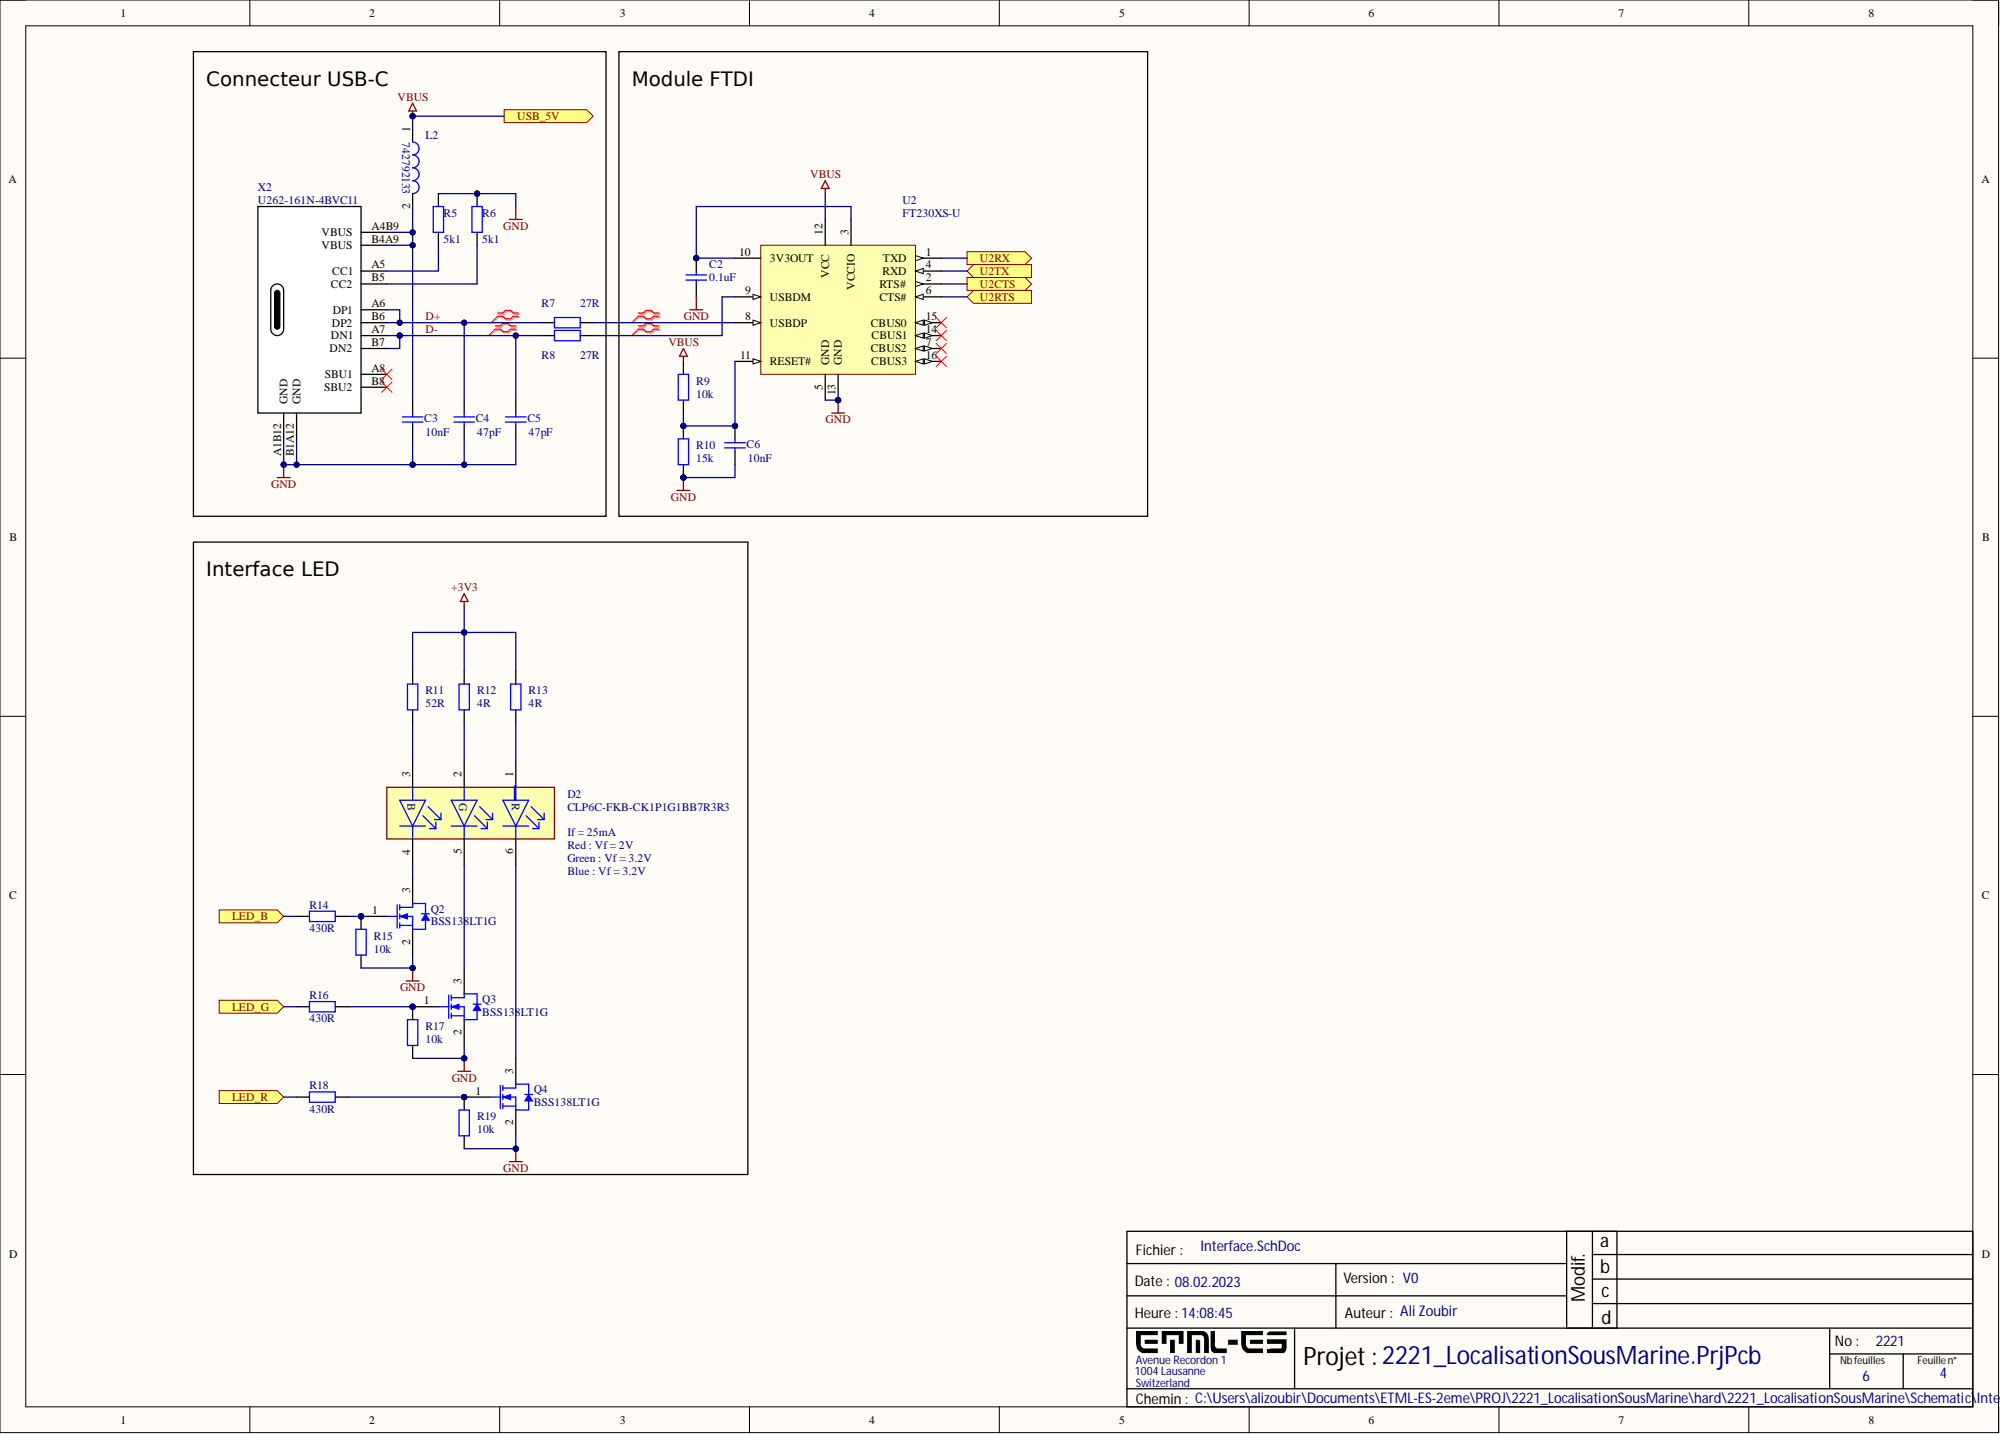
[picture p209: page 3]

GND | USBDP 8

D- | | RESET# 11

Interface.SchDoc Fichier : | | a

Avenue Recordon 1 1004 Lausanne Switzerland | Projet : 2221_LocalisationSousMarine.PrjPcb

Nb feuilles 6 | Feuille n° 4

Chemin : C:\Users\alizoubir\Documents\ETML-ES-2eme\PROJ\2221_LocalisationSousMarine\hard\2221_LocalisationSousMarine\Schematic\Interface.SchDoc

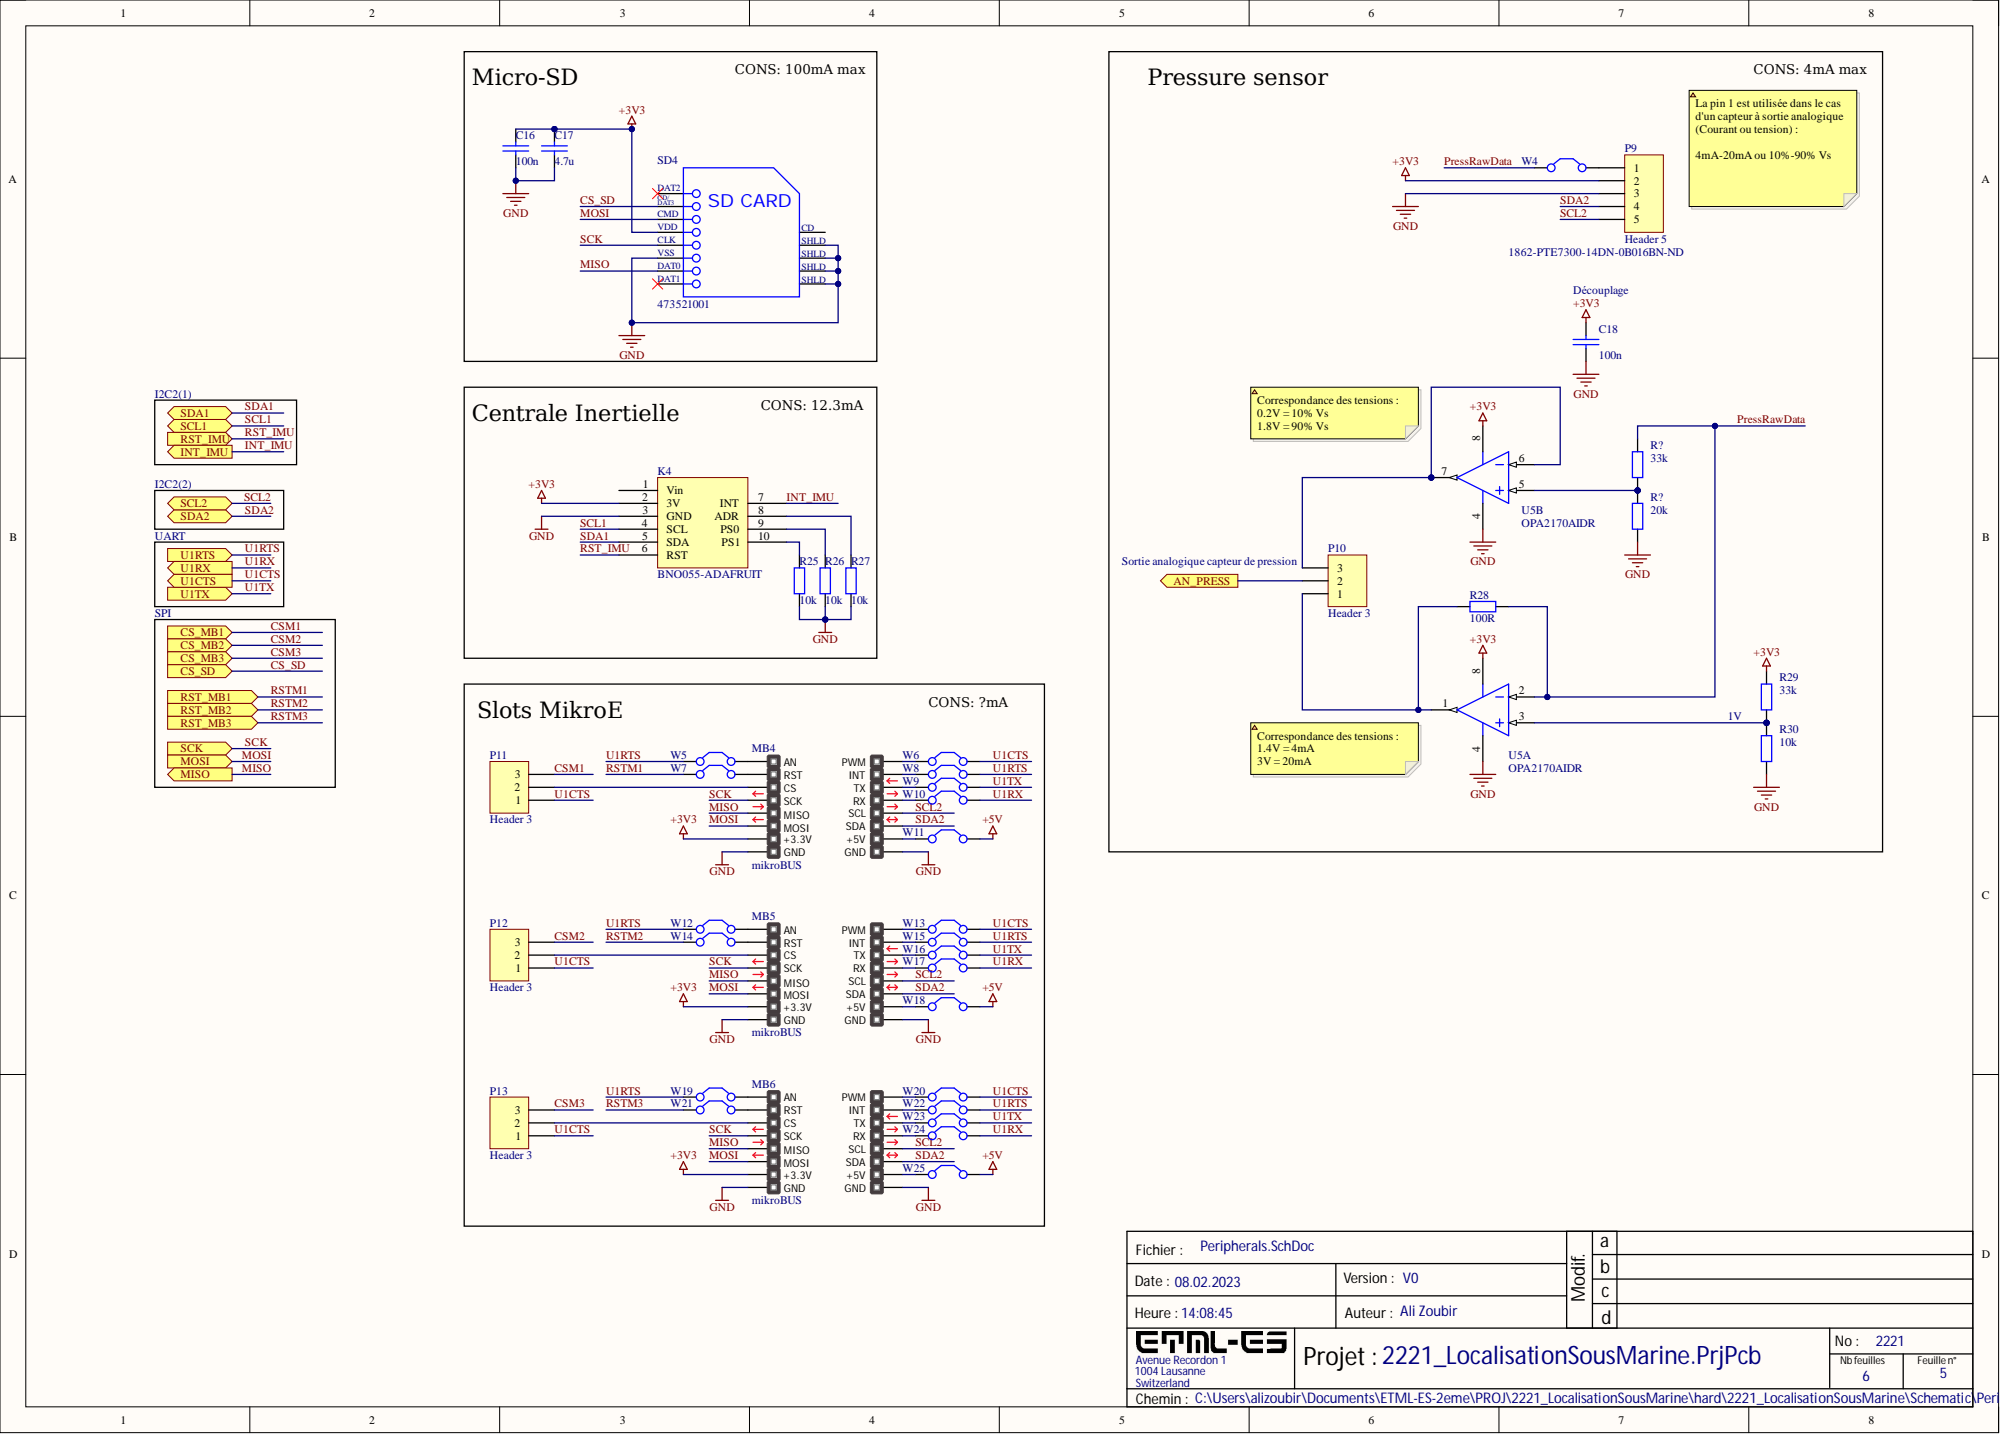
[picture p210: page 4]

1 0

Peripherals. SchDoc Fichier :

Date : 08.02.2023 | Version : V0

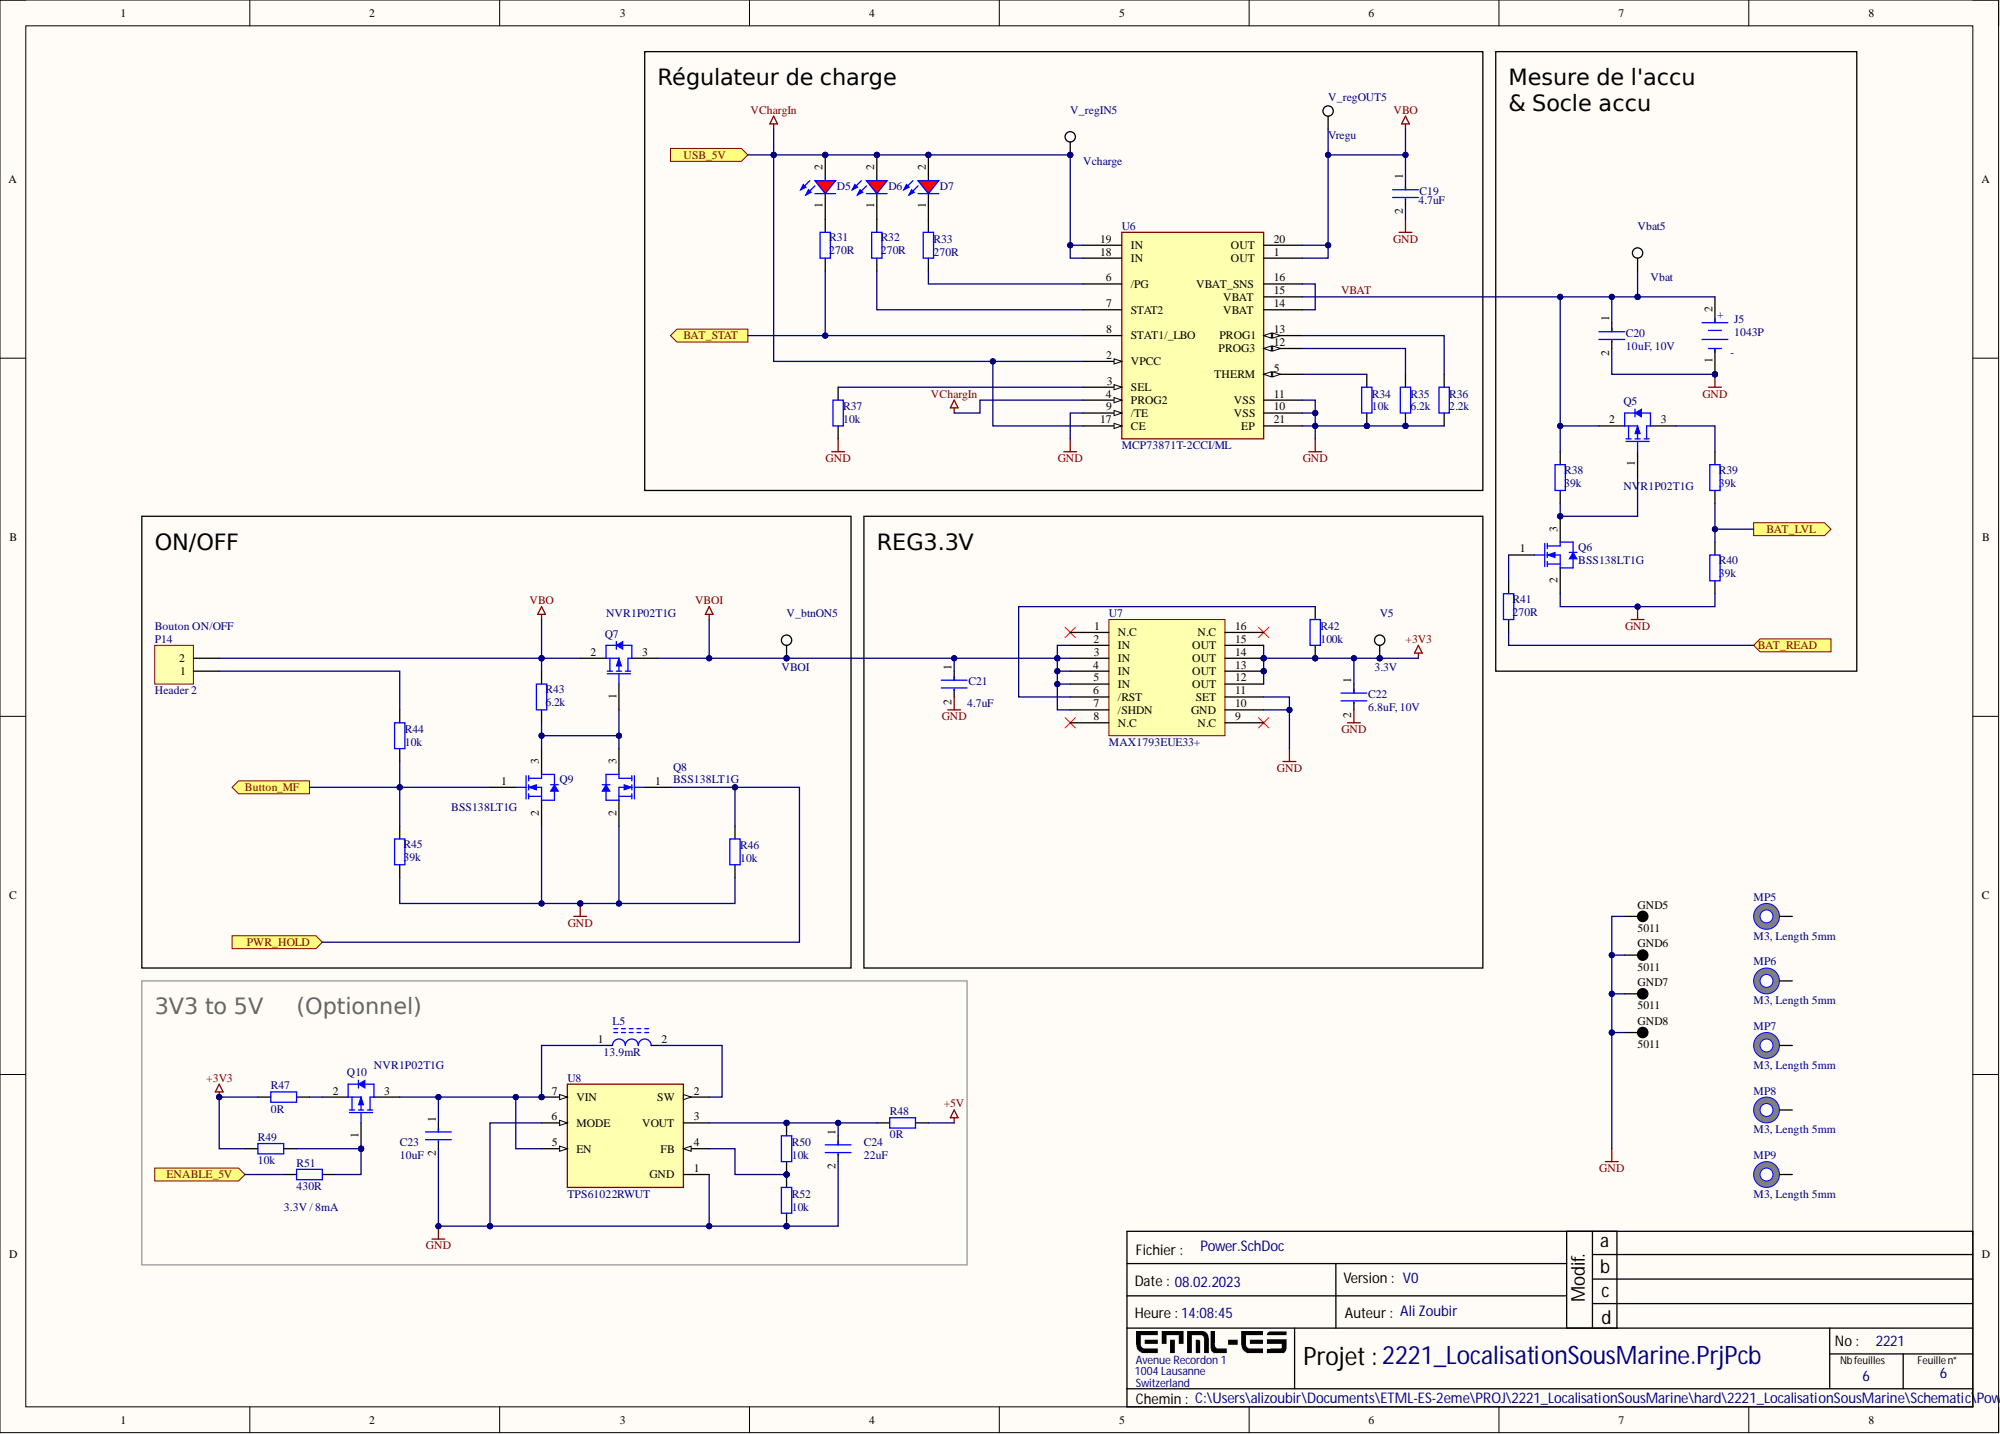
[picture p211: page 5]

IN 4
IN 5
/RST 6
/SHDN 7

Power.SchDoc Fichier : | | a

Avenue Recordon 1 1004 Lausanne Switzerland | Projet : 2221_LocalisationSousMarine.PrjPcb

Nb feuilles 6 | Feuille n° 6

Chemin : C:\Users\alizoubir\Documents\ETML-ES-2eme\PROJ\2221_LocalisationSousMarine\hard\2221_LocalisationSousMarine\Schematic\Power.SchDoc
