Ali-Z0/2221_Underwater-Positioning-System/doc/2221_Implémentation.PDF

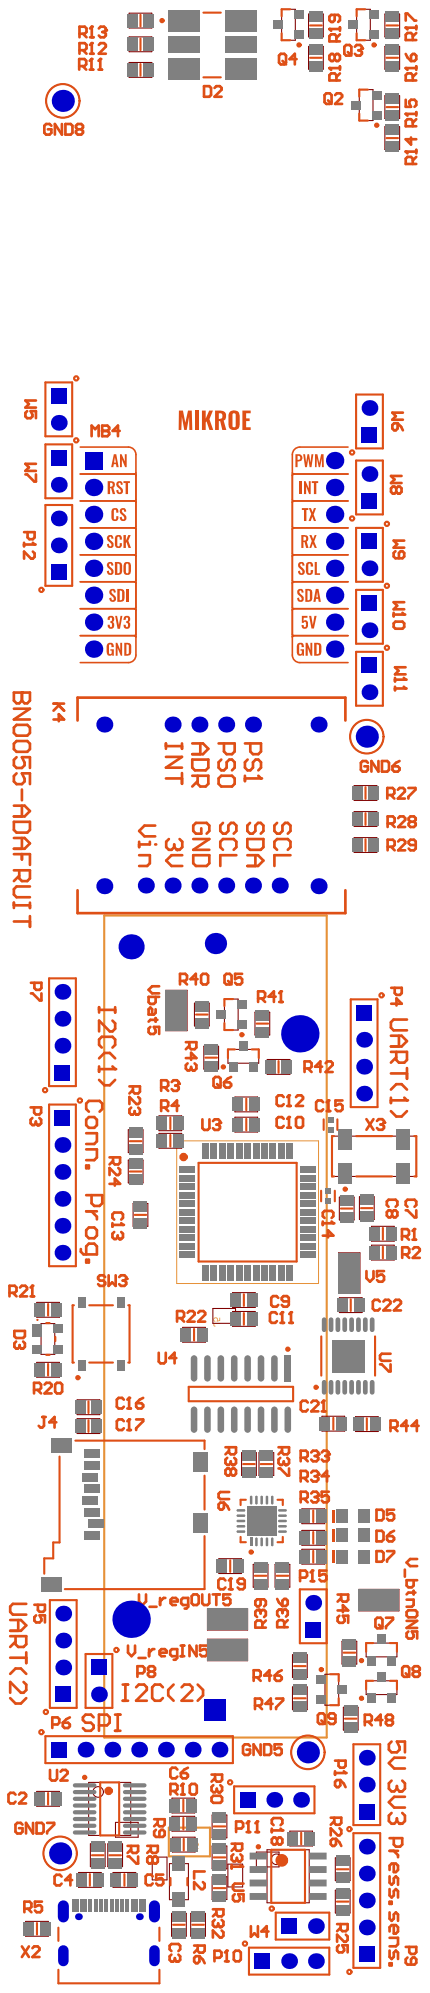
[picture p212: page 1]

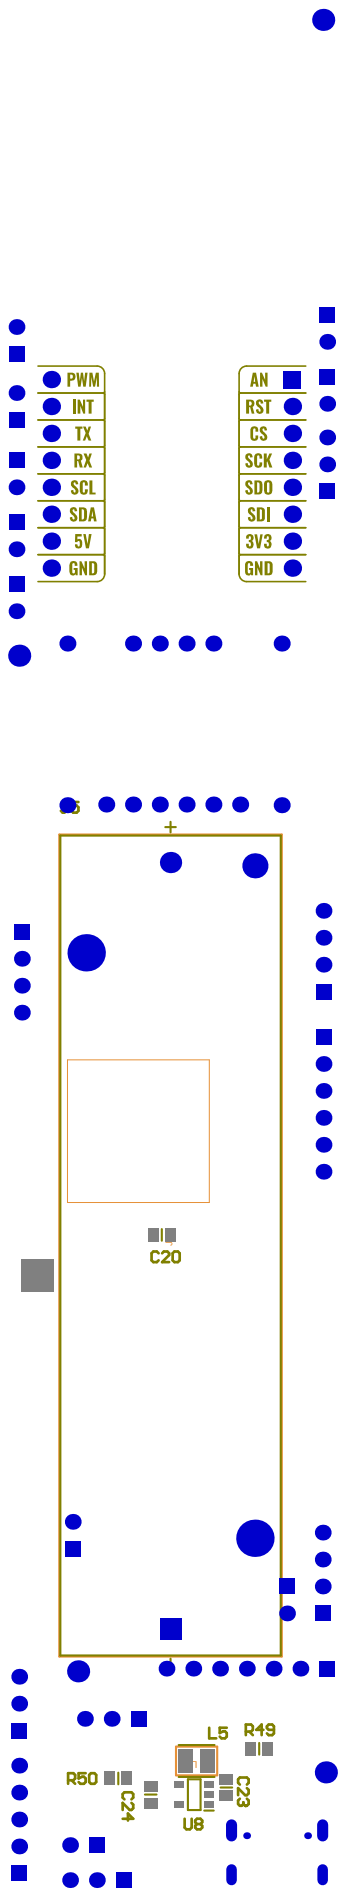
[picture p213: page 2]
