Ali-Z0/2221_Underwater-Positioning-System/hard/2221_LocalisationSousMarine/2221_LocalisationSousMarine.pdf

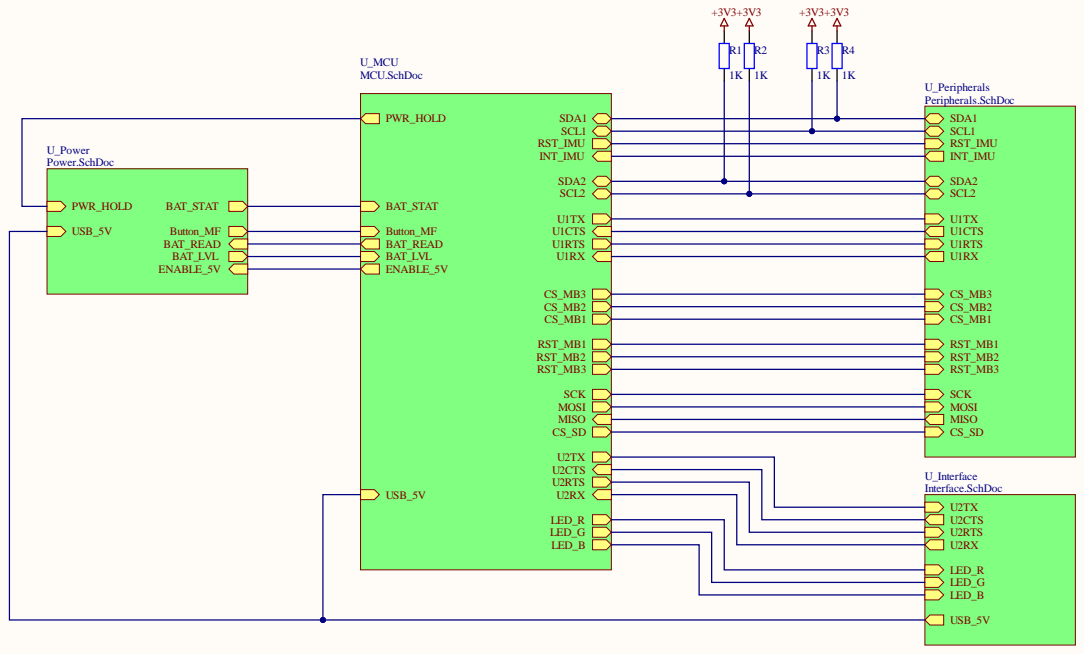
[picture p214: page 1]

abcd

SchemaBloc. SchDoc Fichie r :

Date : 2 6/01 / 2023 | Ve rsion : V0

H eure : 20: 2 5 : 35 | Auteur : Ali Zoubir
Aven ue Reco rd o n 1 1004 Lausanne Swi tzer l a d | Projet : 2221_Localisat ionSousMarine.PrjPcb | No

N b feuilles | Feuille n°

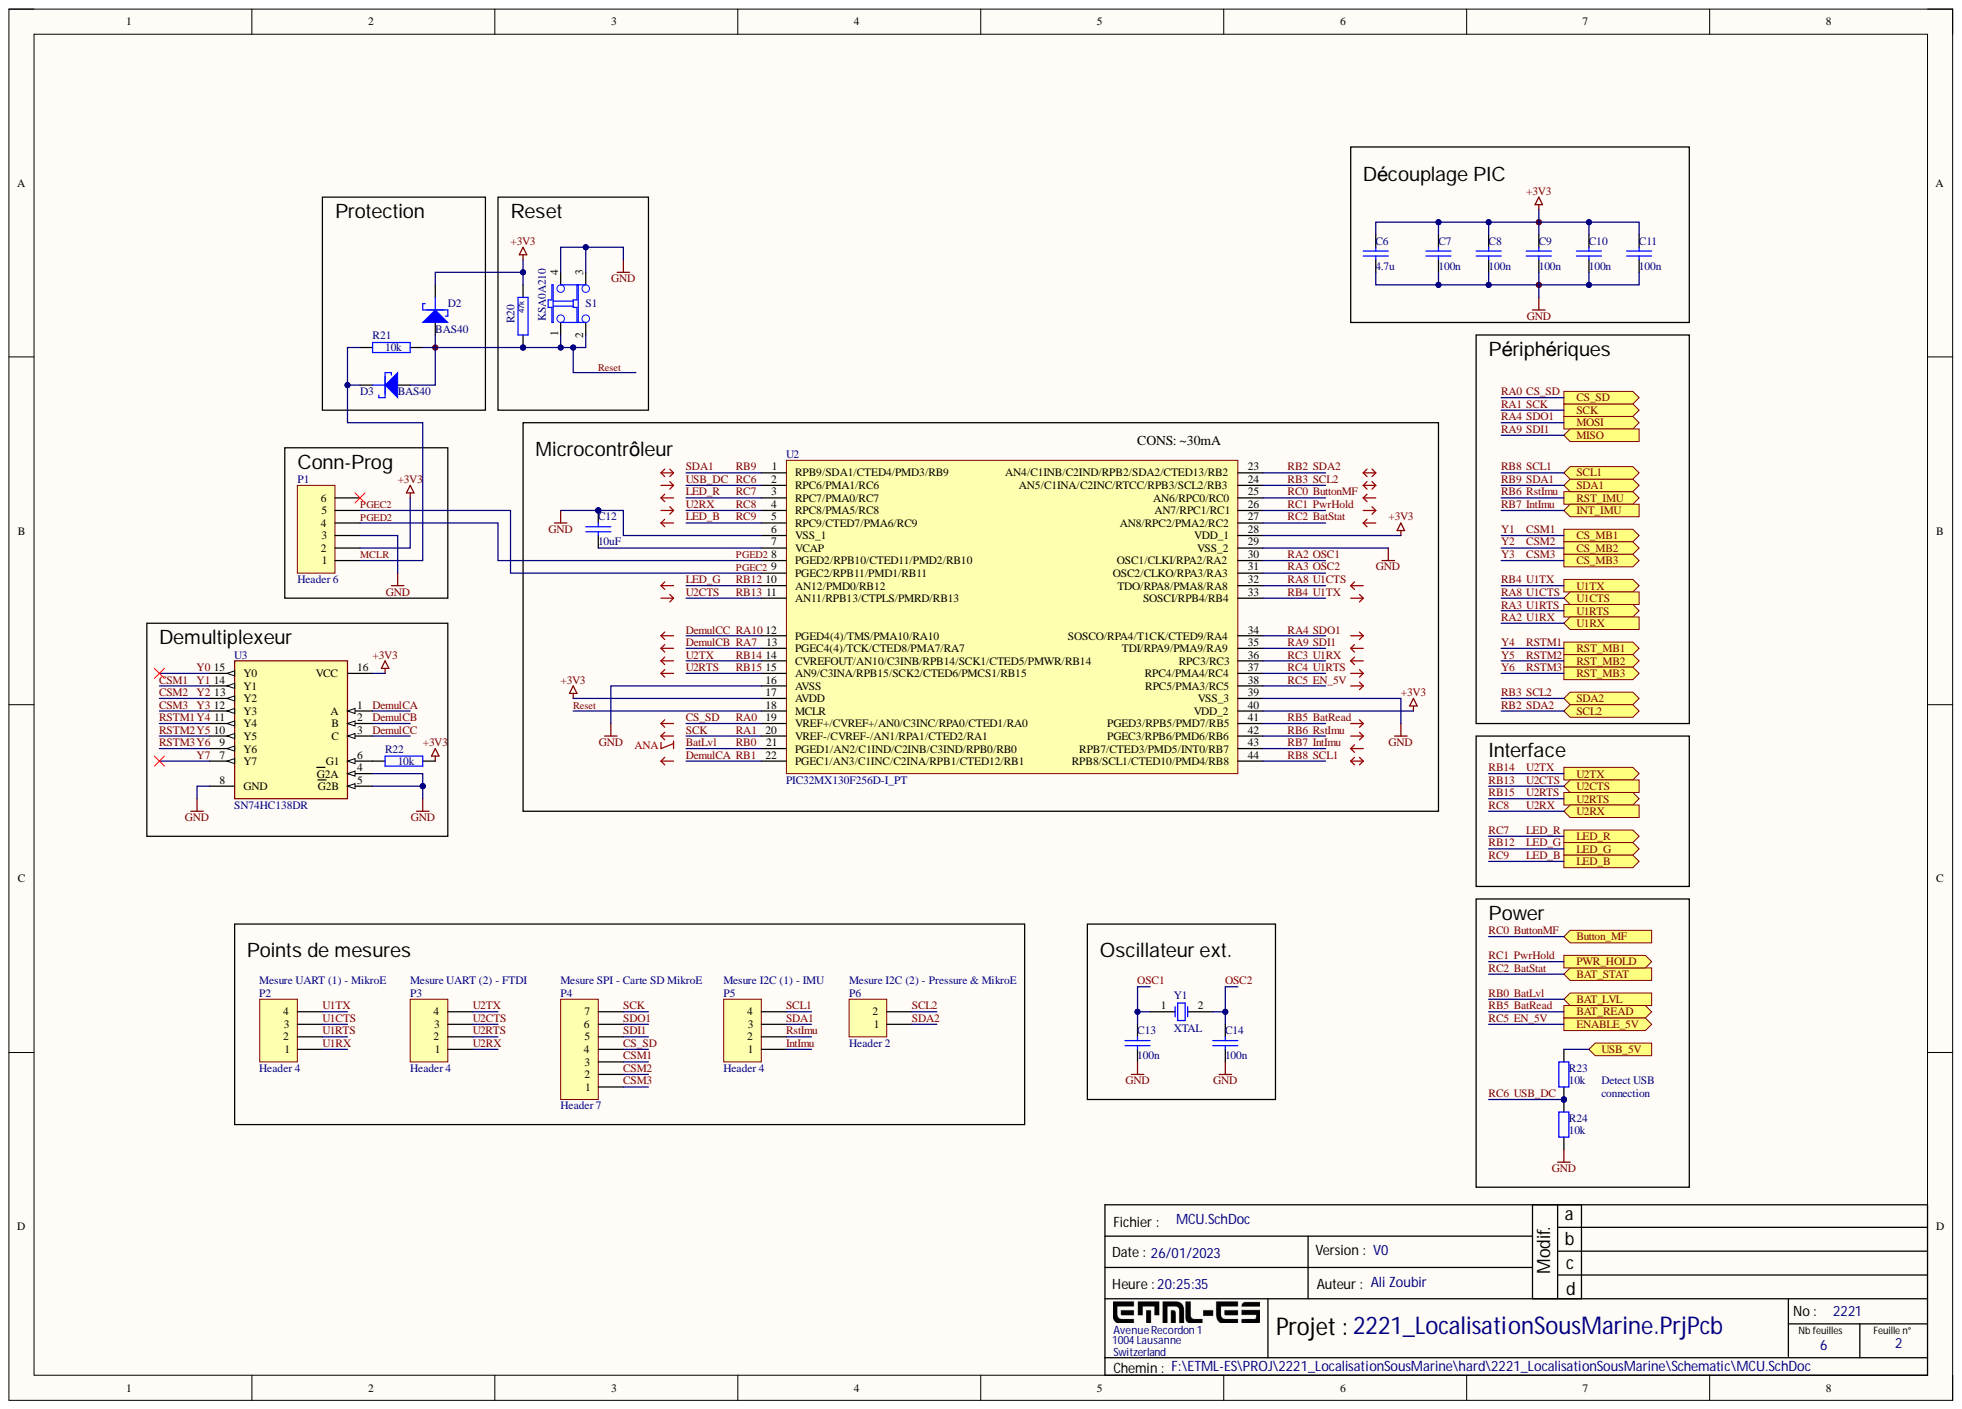
[picture p215: page 2]

MCLR PGED2 PGEC2 | C12 LE D_B R C 9 | 5

abcd

M CU. SchDoc Fichie r :

Date : 2 6/01 / 2023 | Ve rsion : V0

H eure : 20: 2 5 : 35 | Auteur : Ali Zoubir

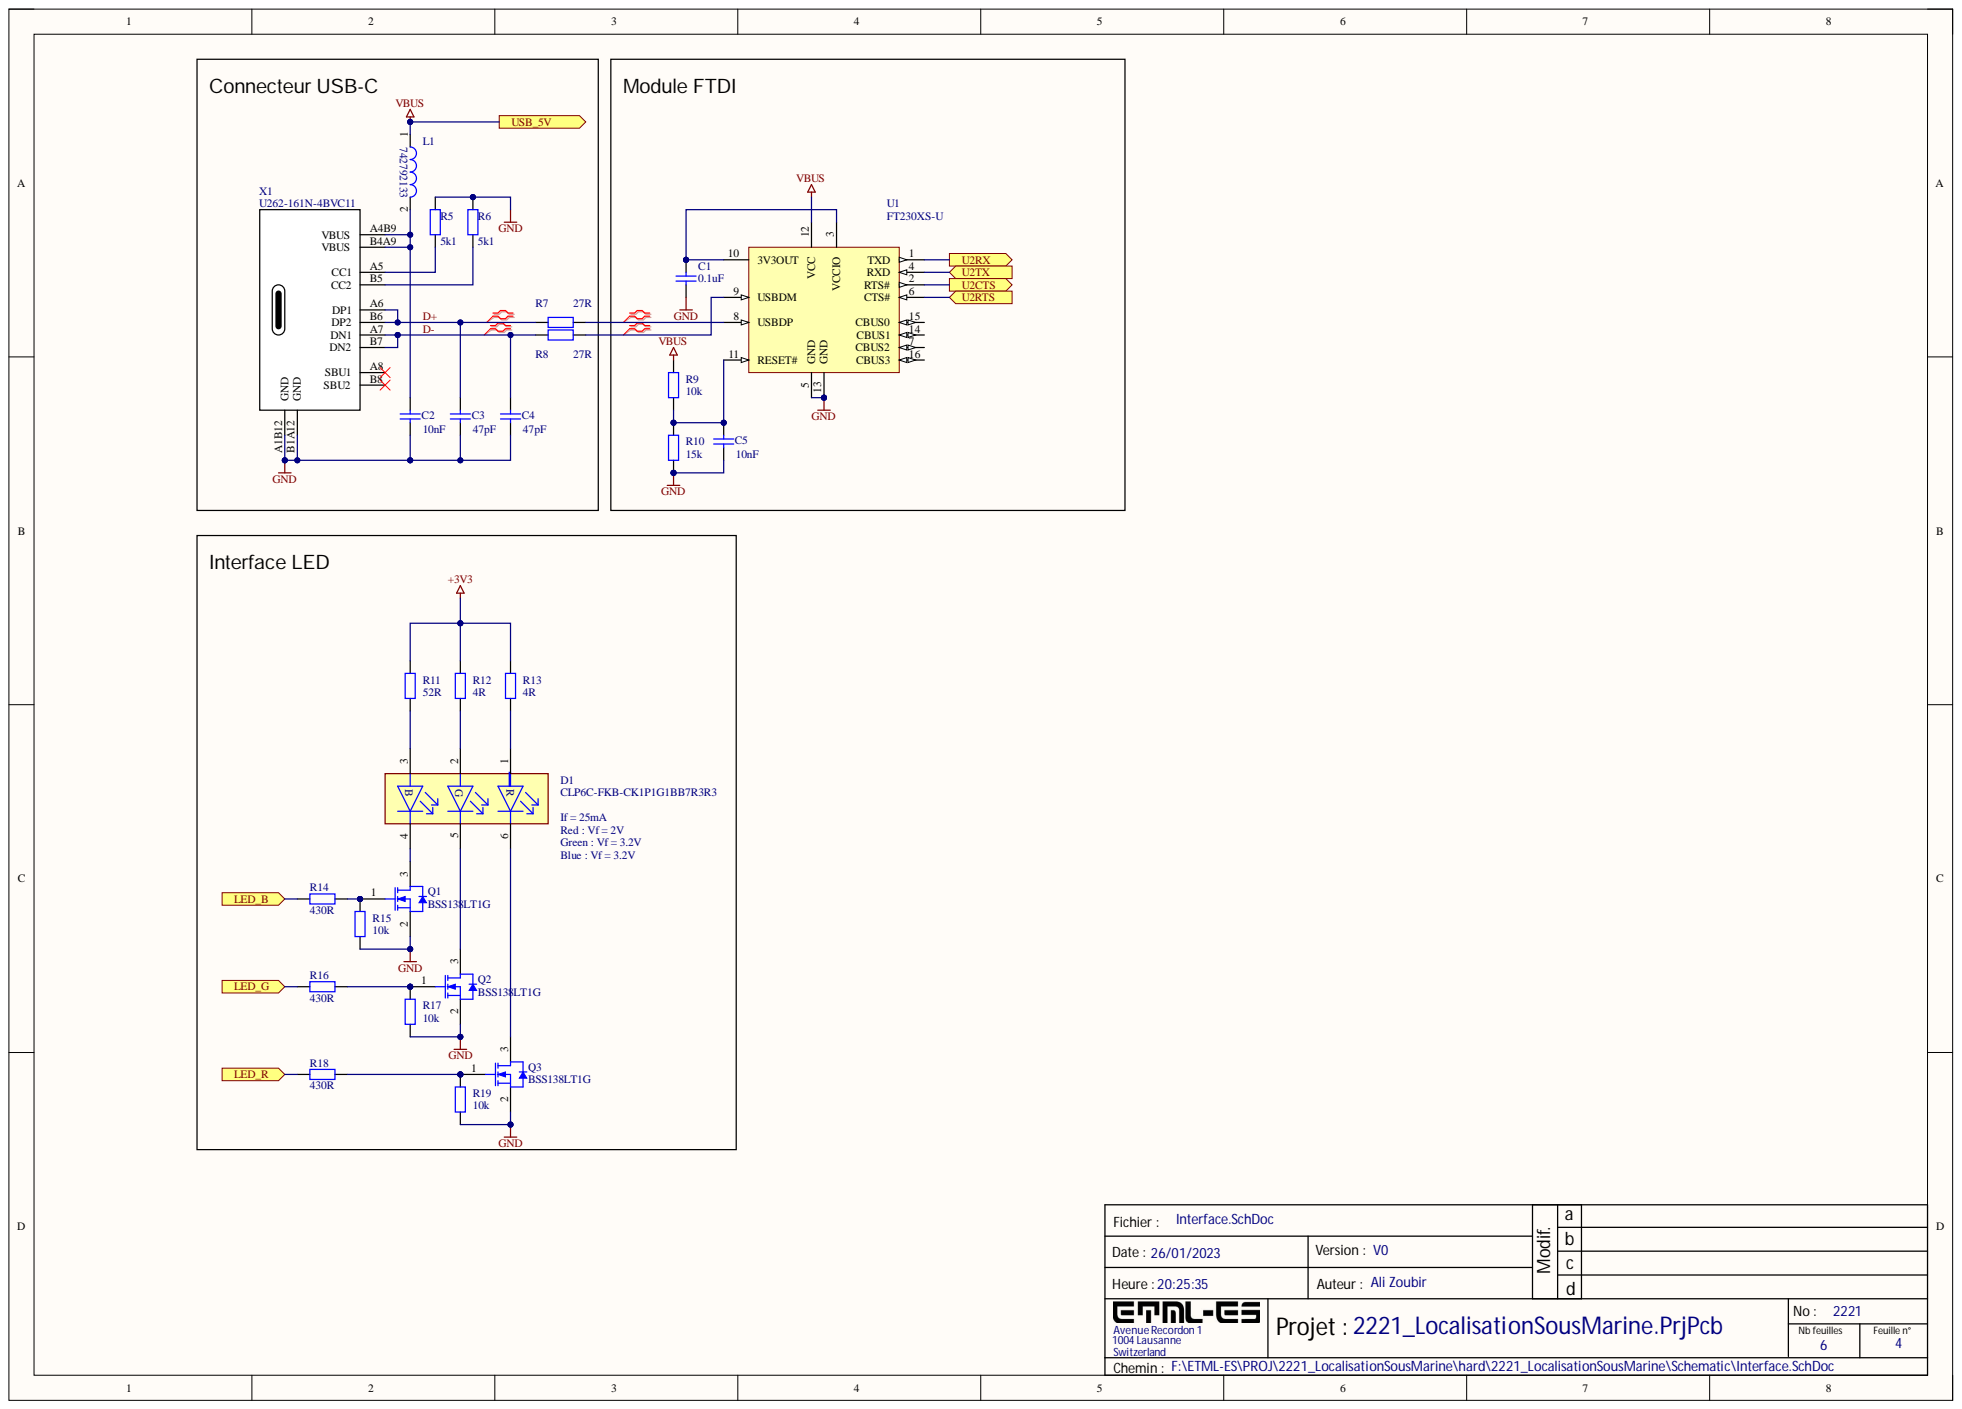
[picture p216: page 3]

GND | USBDP 8

D- | | RESET# 11

Interface.SchDoc Fichier : | | a

Date : 26/01/2023 | Version : V0

Heure : 20:25:35 | Auteur : Ali Zoubir
Avenue Recordon 1 1004 Lausanne Switzerland | Projet : 2221_LocalisationSousMarine.PrjPcb | No : 2221

Nb feuilles 6 | Feuille n° 4

Chemin : F:\ETML-ES\PROJ\2221_LocalisationSousMarine\hard\2221_LocalisationSousMarine\Schematic\Interface.SchDoc

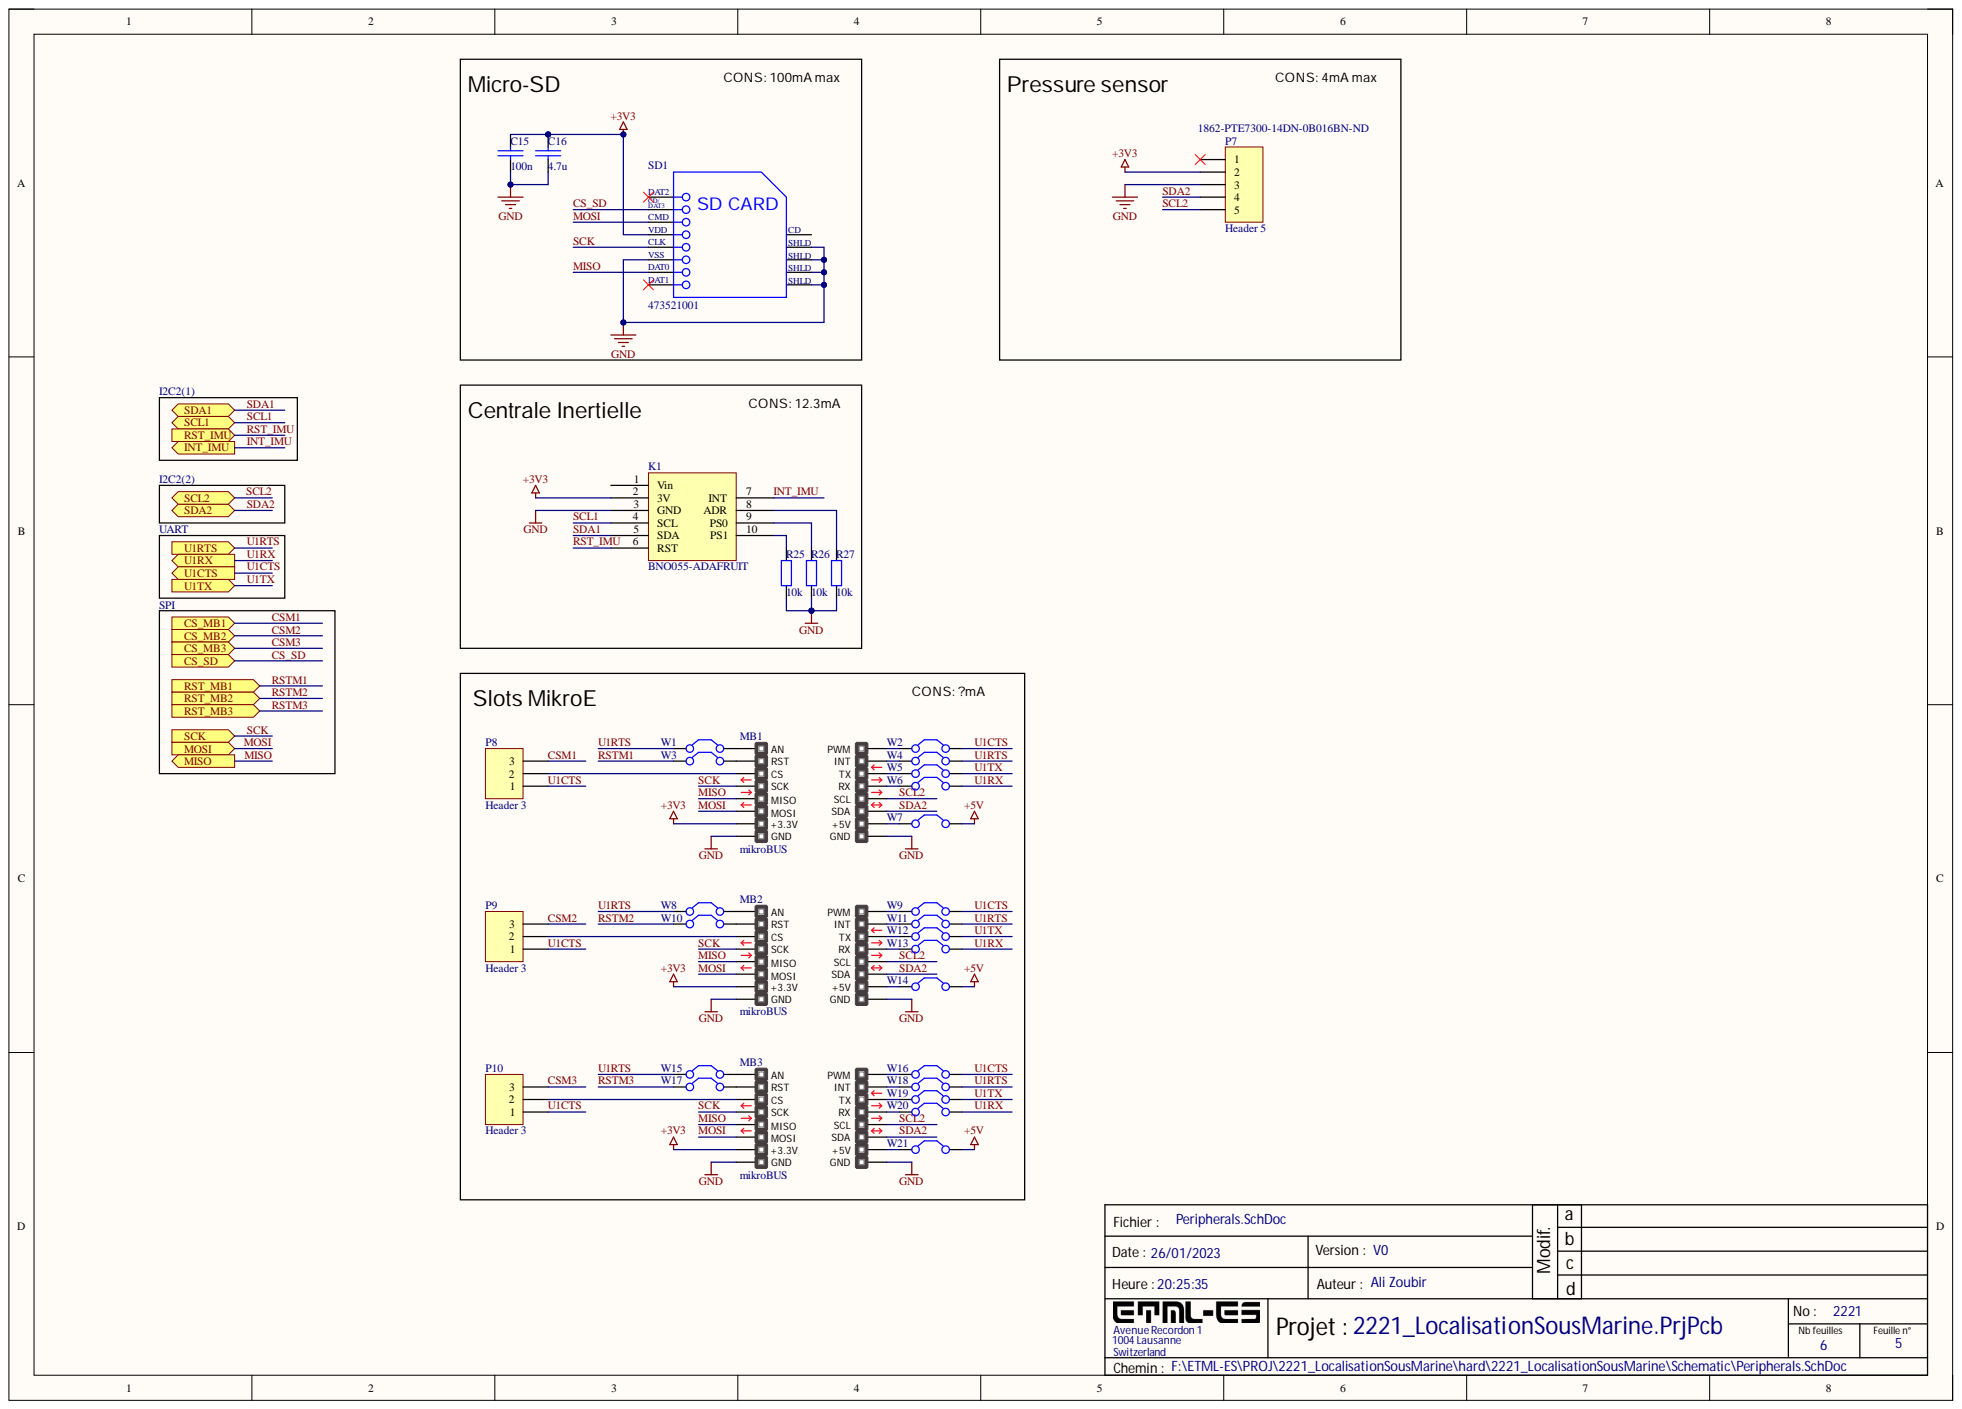
[picture p217: page 4]

abcd

Pe riphe rals. SchDoc Fichie r :

Date : 2 6/01 / 2023 | Ve rsion : V0

H eure : 20: 2 5 : 35 | Auteur : Ali Zoubir

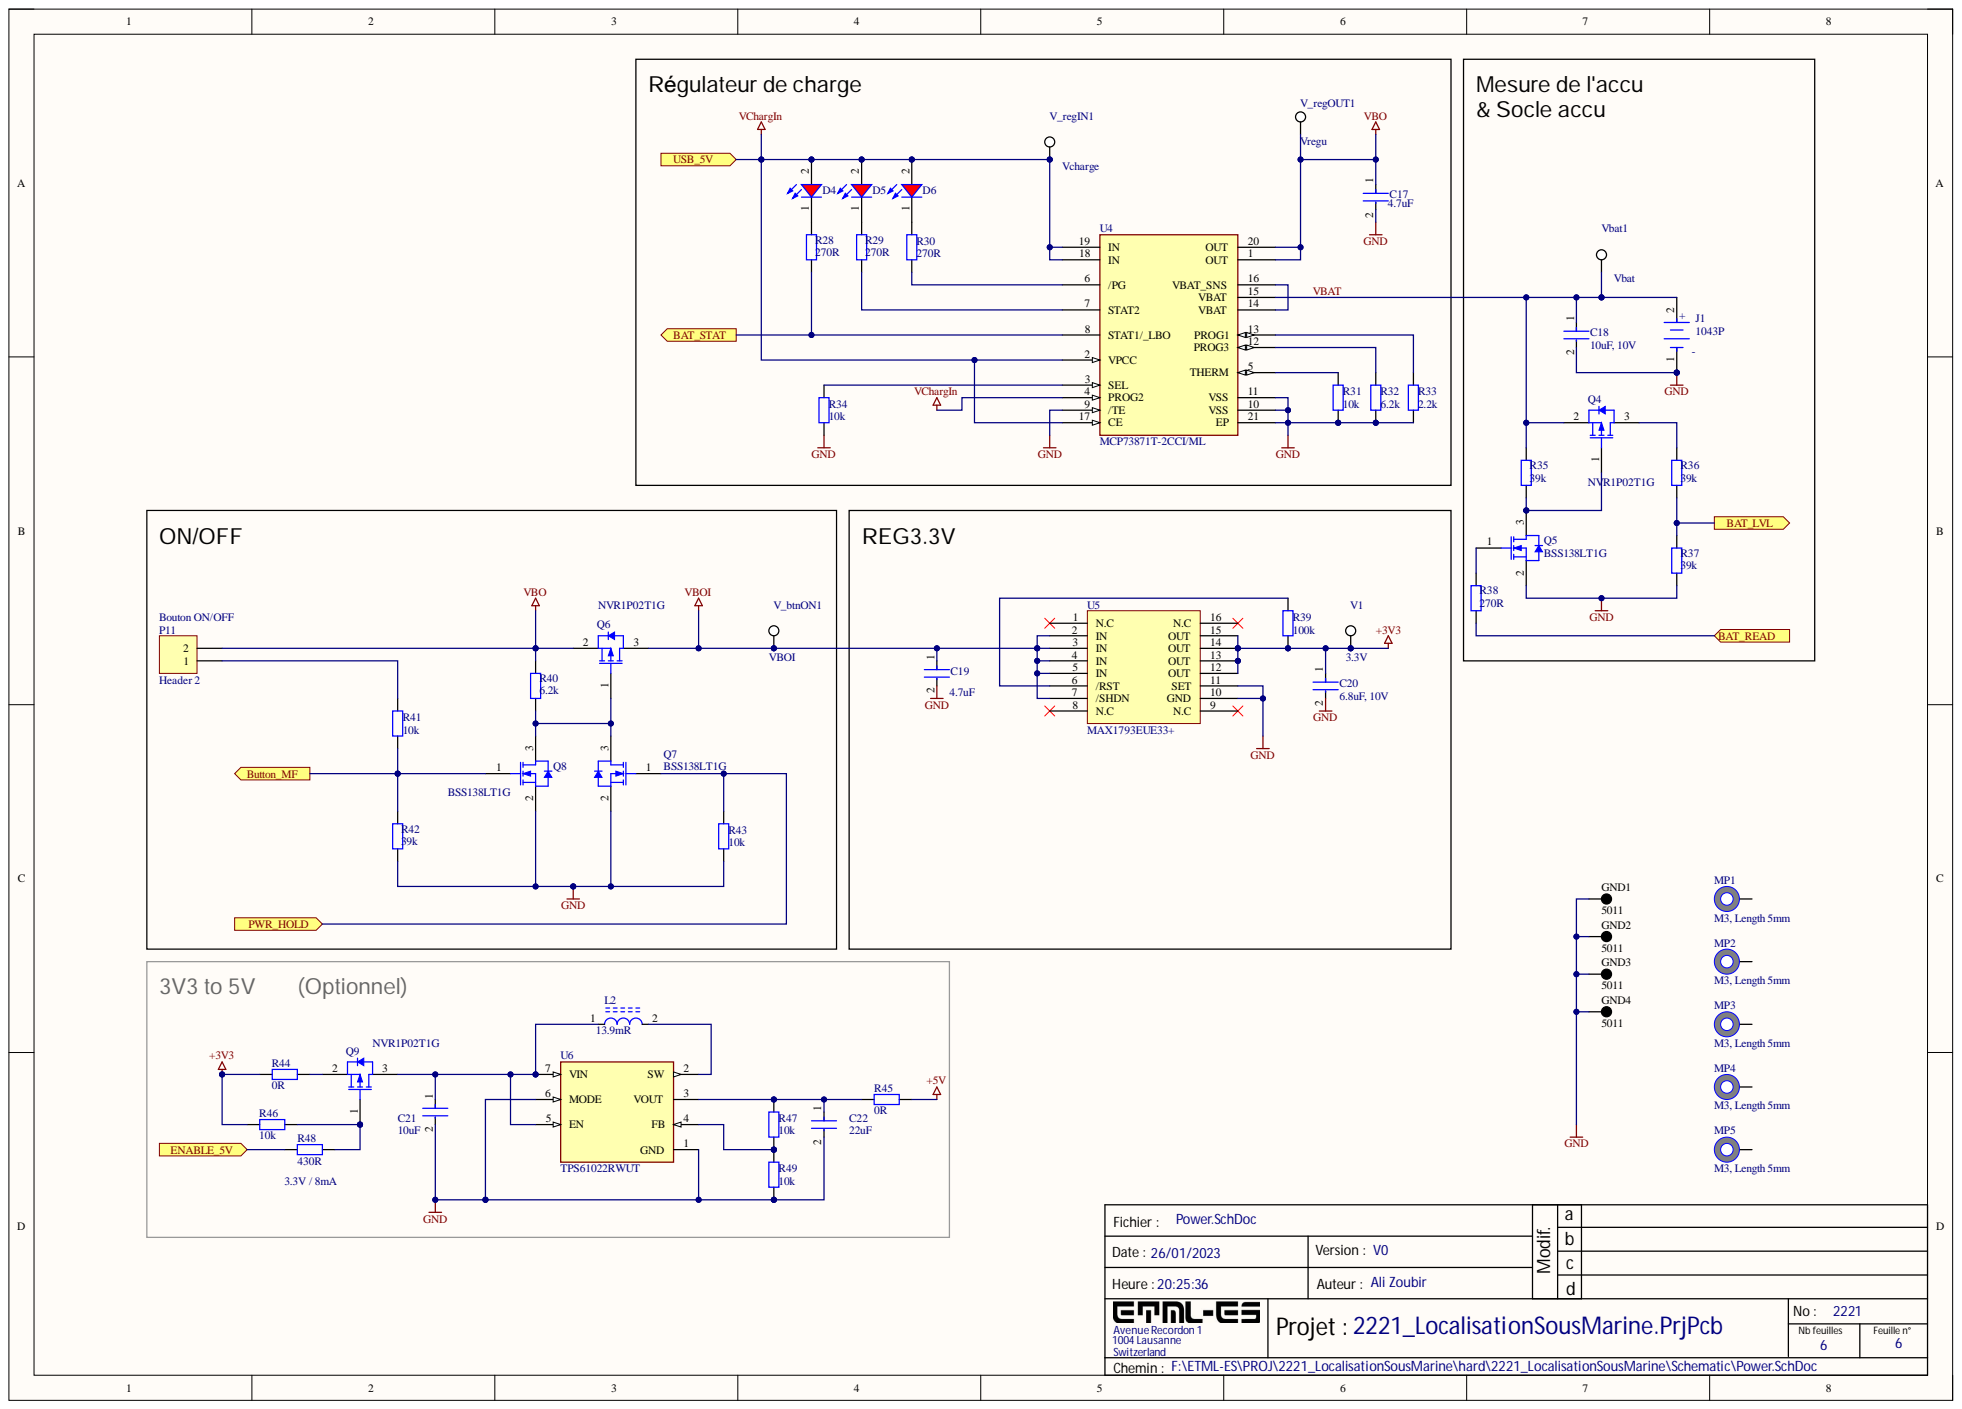
[picture p218: page 5]

7 | /SH D N G N N.C N.C

abcd

Powe r. SchDoc Fichie r :

Date : 2 6/01 / 2023 | Ve rsion : V0

H eure : 20: 2 5 : 36 | Auteur : Ali Zoubir
