Ali-Z0/2221_Underwater-Positioning-System/doc/Presentations/Pre-etude/Pré-étude/Images/logo-eps-converted-to.pdf

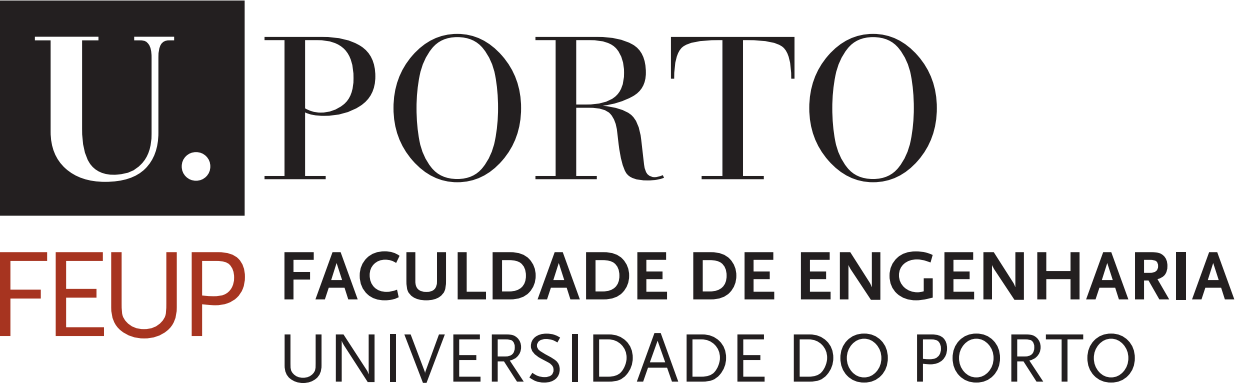
[picture p219: page 1]
