Ali-Z0/2221_Underwater-Positioning-System/hard/Simulations/Amplis.asc

I1: current; 20m
R1: res; 68k
R2: res; 47k
R3: res; 43k
R4: res; 68k
R5: res; 100
R6: res; 100k
R7: res; 100k
U3: opamp
U4: opamp
V2: voltage; 2.9
Named nets: 0, 3V3
.tran 5m
