Ali-Z0/2221_Underwater-Positioning-System/soft/Code-Principale/firmware/src/app.h

/*******************************************************************************
  MPLAB Harmony Application Header File

  Company:
    Microchip Technology Inc.

  File Name:
    app.h

  Summary:
    This header file provides prototypes and definitions for the application.

  Description:
    This header file provides function prototypes and data type definitions for
    the application.  Some of these are required by the system (such as the
    "APP_Initialize" and "APP_Tasks" prototypes) and some of them are only used
    internally by the application (such as the "APP_STATES" definition).  Both
    are defined here for convenience.
*******************************************************************************/

//DOM-IGNORE-BEGIN
/*******************************************************************************
Copyright (c) 2013-2014 released Microchip Technology Inc.  All rights reserved.

Microchip licenses to you the right to use, modify, copy and distribute
Software only when embedded on a Microchip microcontroller or digital signal
controller that is integrated into your product or third party product
(pursuant to the sublicense terms in the accompanying license agreement).

You should refer to the license agreement accompanying this Software for
additional information regarding your rights and obligations.

SOFTWARE AND DOCUMENTATION ARE PROVIDED "AS IS" WITHOUT WARRANTY OF ANY KIND,
EITHER EXPRESS OR IMPLIED, INCLUDING WITHOUT LIMITATION, ANY WARRANTY OF
MERCHANTABILITY, TITLE, NON-INFRINGEMENT AND FITNESS FOR A PARTICULAR PURPOSE.
IN NO EVENT SHALL MICROCHIP OR ITS LICENSORS BE LIABLE OR OBLIGATED UNDER
CONTRACT, NEGLIGENCE, STRICT LIABILITY, CONTRIBUTION, BREACH OF WARRANTY, OR
OTHER LEGAL EQUITABLE THEORY ANY DIRECT OR INDIRECT DAMAGES OR EXPENSES
INCLUDING BUT NOT LIMITED TO ANY INCIDENTAL, SPECIAL, INDIRECT, PUNITIVE OR
CONSEQUENTIAL DAMAGES, LOST PROFITS OR LOST DATA, COST OF PROCUREMENT OF
SUBSTITUTE GOODS, TECHNOLOGY, SERVICES, OR ANY CLAIMS BY THIRD PARTIES
(INCLUDING BUT NOT LIMITED TO ANY DEFENSE THEREOF), OR OTHER SIMILAR COSTS.
 *******************************************************************************/
//DOM-IGNORE-END

#ifndef _APP_H
#define _APP_H

// *****************************************************************************
// *****************************************************************************
// Section: Included Files
// *****************************************************************************
// *****************************************************************************

#include <stdint.h>
#include <stdbool.h>
#include <stddef.h>
#include <stdlib.h>
#include "system_config.h"
#include "system_definitions.h"
#include "bno055.h"

// DOM-IGNORE-BEGIN
#ifdef __cplusplus  // Provide C++ Compatibility

extern "C" {

#endif
// DOM-IGNORE-END 
    
#define TIME_OUT 80000000U
#define TIME_POWER_OFF   500

// *****************************************************************************
// *****************************************************************************
// Section: Type Definitions
// *****************************************************************************
// *****************************************************************************
typedef struct {
    s32 comres;
    bool flagMeasReady;
    uint8_t flagImportantMeas;
    struct bno055_gravity_double_t gravity;
    struct bno055_linear_accel_double_t linear_accel;
    struct bno055_euler_double_t euler;
    struct bno055_gyro_double_t gyro;
    struct bno055_mag_double_t mag;
    struct bno055_quaternion_t quaternion;
    unsigned long time;
    unsigned long l_time;
    uint16_t d_time;
    float pressure;
}s_bno055_data;
// *****************************************************************************
/* Application states

  Summary:
    Application states enumeration

  Description:
    This enumeration defines the valid application states.  These states
    determine the behavior of the application at various times.
*/

typedef enum
{
	/* Application's state machine's initial state. */
	APP_STATE_INIT=0,
    APP_STATE_LOGGING,
    APP_STATE_FLAG_MEAS,
	APP_STATE_SHUTDOWN
	/* TODO: Define states used by the application state machine. */

} APP_STATES;


// *****************************************************************************
/* Application Data

  Summary:
    Holds application data

  Description:
    This structure holds the application's data.

  Remarks:
    Application strings and buffers are be defined outside this structure.
 */

typedef struct
{
    /* The application's current state */
    APP_STATES state;
} APP_DATA;

typedef struct
{
    /* Main Timer (1ms) */
    uint32_t mainTmrCnt;
    /* Timer precis (1us) */
    bool TmrTickFlag;
    uint32_t TmrCnt;
    /* Measure todo flag */
    unsigned long TmrMeas;
    unsigned long ltime;
    bool measTodoFlag;
    /* Timer display */
    uint32_t TmrDisplay;
    /* Tmr wait shutdown */
    bool flagCountBtnPressed;
    uint32_t TmrBtnPressed;
}TIMER_DATA;

// *****************************************************************************
// *****************************************************************************
// Section: Application Callback Routines
// *****************************************************************************
// *****************************************************************************
// *****************************************************************************
// *****************************************************************************
// Section: Application Initialization and State Machine Functions
// *****************************************************************************
// *****************************************************************************

/*******************************************************************************
  Function:
    void APP_Initialize ( void )

  Summary:
     MPLAB Harmony application initialization routine.

  Description:
    This function initializes the Harmony application.  It places the 
    application in its initial state and prepares it to run so that its 
    APP_Tasks function can be called.

  Precondition:
    All other system initialization routines should be called before calling
    this routine (in "SYS_Initialize").

  Parameters:
    None.

  Returns:
    None.

  Example:
    <code>
    APP_Initialize();
    </code>

  Remarks:
    This routine must be called from the SYS_Initialize function.
*/

void APP_Initialize ( void );

void prepareBuffer( char * buffer );

void App_resetMeasFlag( void );

/*******************************************************************************
  Function:
    void APP_Tasks ( void )

  Summary:
    MPLAB Harmony Demo application tasks function

  Description:
    This routine is the Harmony Demo application's tasks function.  It
    defines the application's state machine and core logic.

  Precondition:
    The system and application initialization ("SYS_Initialize") should be
    called before calling this.

  Parameters:
    None.

  Returns:
    None.

  Example:
    <code>
    APP_Tasks();
    </code>

  Remarks:
    This routine must be called from SYS_Tasks() routine.
 */

void APP_Tasks( void );


// Callback main timer
void MainTimer_callback( void );

// Callback display timer
void DisplayTimer_callback( void );

#endif /* _APP_H */

//DOM-IGNORE-BEGIN
#ifdef __cplusplus
}
#endif
//DOM-IGNORE-END

/*******************************************************************************
 End of File
 */
