Ali-Z0/2221_Underwater-Positioning-System/soft/Code-Principale/firmware/src/Mc32_PressAdc.h

/* ************************************************************************** */
/** Descriptive File Name

  @Company
    Company Name

  @File Name
    filename.h

  @Summary
    Brief description of the file.

  @Description
    Describe the purpose of this file.
 */
/* ************************************************************************** */

#ifndef _PRESS_ADC_H    /* Guard against multiple inclusion */
#define _PRESS_ADC_H


/* ************************************************************************** */
/* ************************************************************************** */
/* Section: Included Files                                                    */
/* ************************************************************************** */
/* ************************************************************************** */
#include "app.h"
/* This section lists the other files that are included in this file.
 */

/* TODO:  Include other files here if needed. */


/* Provide C++ Compatibility */
#ifdef __cplusplus
extern "C" {
#endif


    /* ************************************************************************** */
    /* ************************************************************************** */
    /* Section: Constants                                                         */
    /* ************************************************************************** */
    /* ************************************************************************** */
#define     V_MIN               0.5
#define     V_MAX               4
#define     P_RANGE             10.0
#define     OPAMP_GAIN          0.5913
#define     ADC_RES             (3.3/1024)
#define     ADC_AN_SCAN_ADDRES  0x0008
    /* ************************************************************************** */
    

    // *****************************************************************************
    // *****************************************************************************
    // Section: Data Types
    // *****************************************************************************
    // *****************************************************************************
    typedef struct{
        uint16_t AN3;
    }S_ADCResults;
    // *****************************************************************************


    // *****************************************************************************
    // *****************************************************************************
    // Section: Interface Functions
    // *****************************************************************************
    // *****************************************************************************

    /* Convert voltage into pressure in [Bar] */
    float Press_voltageToPressure(float voltage);
    
    /* Convert raw adc value to voltage */
    float Press_RawToVoltage(float raw);
    
    void Press_InitADC (void);
    
    S_ADCResults Press_ReadAllADC( void );
    
    float Press_readPressure( void );
    // *****************************************************************************
    


    /* Provide C++ Compatibility */
#ifdef __cplusplus
}
#endif

#endif /* _EXAMPLE_FILE_NAME_H */

/* *****************************************************************************
 End of File
 */
